john-luan/SDR-dongle/hardware/PL_Config.kicad_sch

## KiCad design hardware/PL_Config.kicad_sch (2022-02-24)

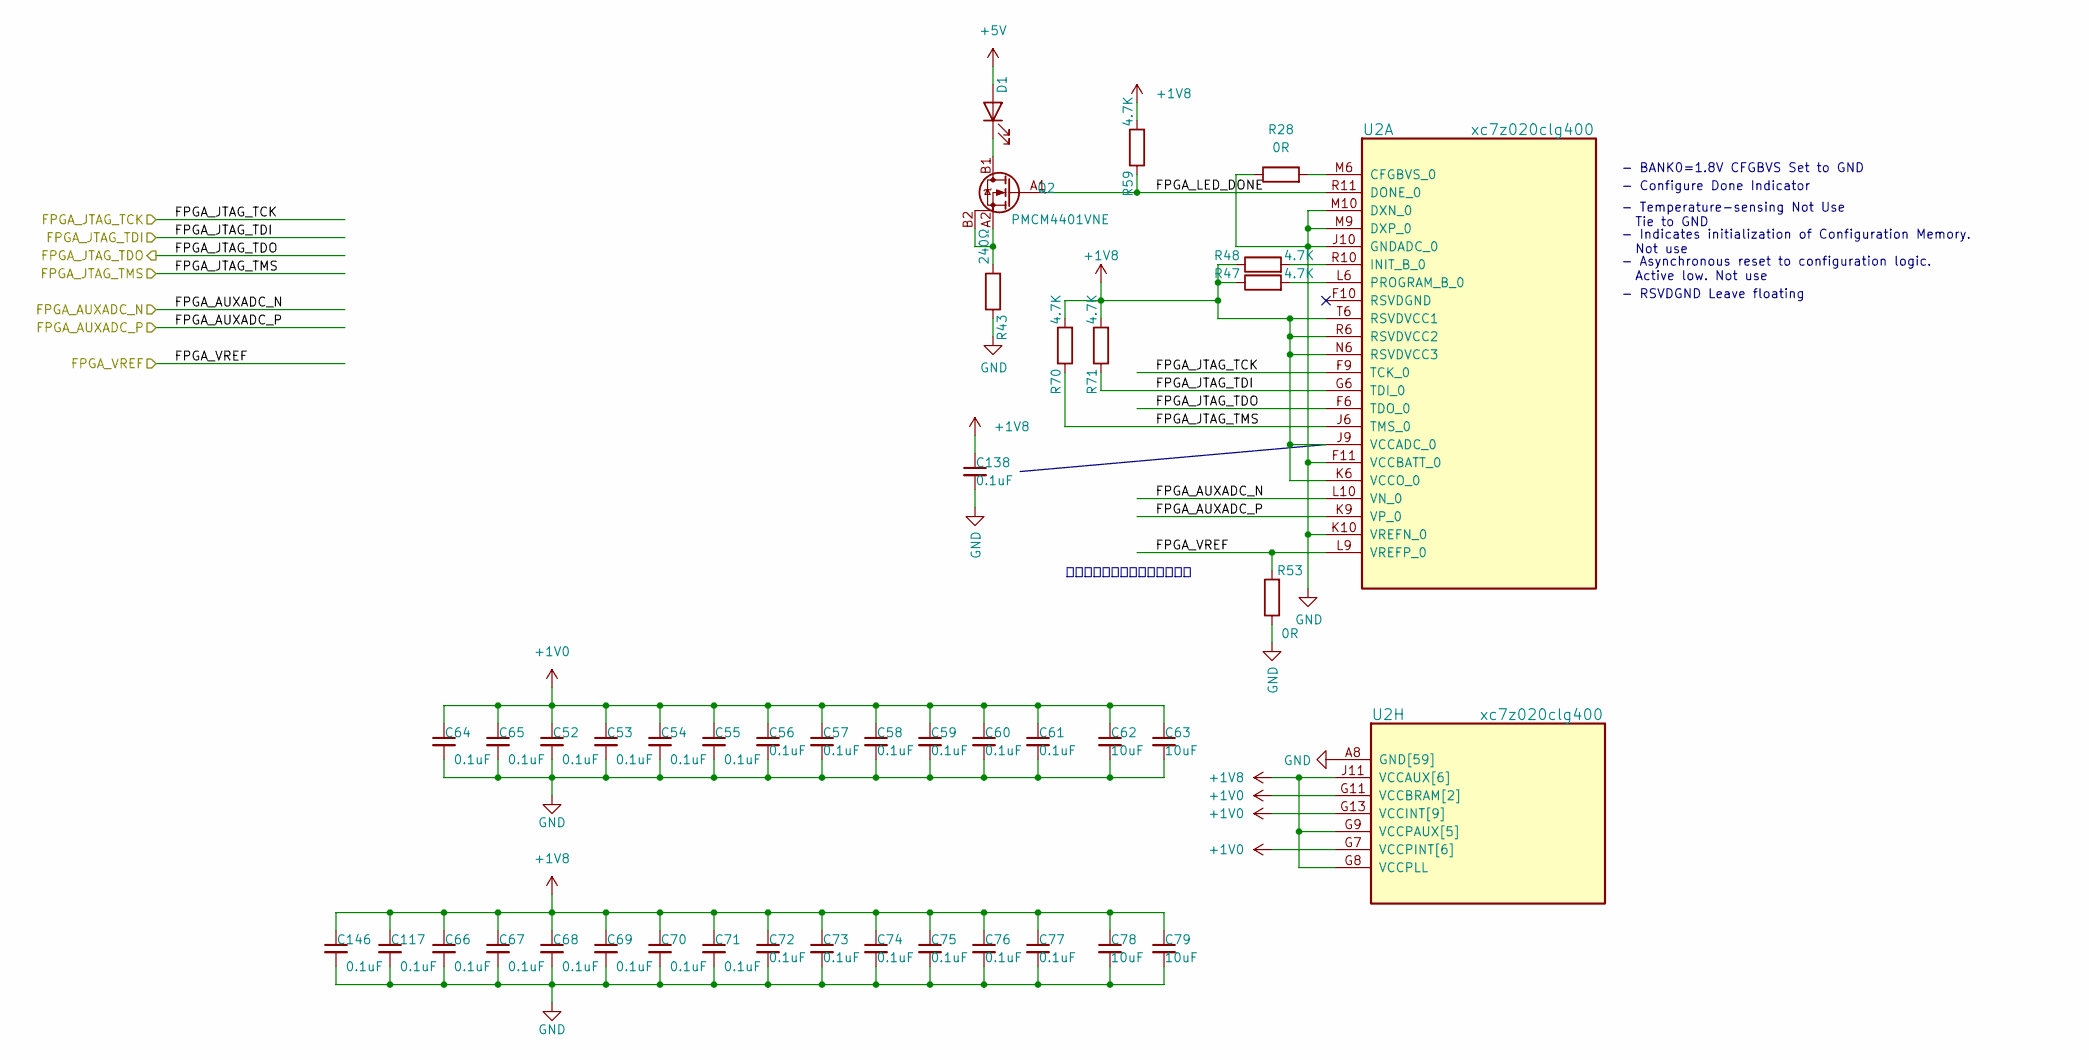
[picture p23: schematic PL_Config.kicad_sch]

Parts:
C52, C53, C54, C55, C56, C57, C58, C59, C60, C61, C64, C65, C66, C67, C68, C69, C70, C71, C72, C73, C74, C75, C76, C77, C117, C138, C146: 0.1uF; C_0201_0603Metric
C62, C63, C78, C79: 10uF; C_0402_1005Metric
D1: LED; LED_0201_0603Metric
Q2: PMCM4401VNE; WLCSP-4-X1-WLB0909-4_0.89x0.89mm_P0.5mm
R28, R53: 0R; R_0201_0603Metric
R43: 240Ω; R_0201_0603Metric
R47, R48, R59, R70, R71: 4.7K; R_0201_0603Metric
U2: xc7z020clg400; Xilinx_CLG400_020_Delay

Connections:
+1V0: C52.1, C53.1, C54.1, C55.1, C56.1, C57.1, C58.1, C59.1, C60.1, C61.1, C62.1, C63.1, C64.1, C65.1, U2.G7 (VCCPINT[6]), U2.G11 (VCCBRAM[2]), U2.G13 (VCCINT[9]), U2.H10 (VCCBRAM[2]), U2.H12 (VCCINT[9]), U2.J7 (VCCPINT[6]), U2.J13 (VCCINT[9]), U2.K12 (VCCINT[9]), U2.L7 (VCCPINT[6]), U2.L13 (VCCINT[9]), U2.M12 (VCCINT[9]), U2.N7 (VCCPINT[6]), U2.N13 (VCCINT[9]), U2.P8 (VCCPINT[6]), U2.P12 (VCCINT[9]), U2.R7 (VCCPINT[6]), U2.R13 (VCCINT[9])
+1V8: C66.1, C67.1, C68.1, C69.1, C70.1, C71.1, C72.1, C73.1, C74.1, C75.1, C76.1, C77.1, C78.1, C79.1, C117.1, C138.1, C146.1, R47.1, R48.1, R59.2, R70.2, R71.2, U2.F8 (VCCPAUX[5]), U2.G8 (VCCPLL), U2.G9 (VCCPAUX[5]), U2.H8 (VCCPAUX[5]), U2.J9 (VCCADC_0), U2.J11 (VCCAUX[6]), U2.K6 (VCCO_0), U2.K8 (VCCPAUX[5]), U2.L11 (VCCAUX[6]), U2.M8 (VCCPAUX[5]), U2.N6 (RSVDVCC3), U2.N9 (VCCAUX[6]), U2.N11 (VCCAUX[6]), U2.P10 (VCCAUX[6]), U2.R6 (RSVDVCC2), U2.R9 (VCCAUX[6]), U2.T6 (RSVDVCC1)
+5V: D1.2 (A)
FPGA_AUXADC_N: U2.L10 (VN_0)
FPGA_AUXADC_P: U2.K9 (VP_0)
FPGA_JTAG_TCK: U2.F9 (TCK_0)
FPGA_JTAG_TDI: R71.1, U2.G6 (TDI_0)
FPGA_JTAG_TDO: U2.F6 (TDO_0)
FPGA_JTAG_TMS: R70.1, U2.J6 (TMS_0)
FPGA_LED_DONE: Q2.A1 (G), R59.1, U2.R11 (DONE_0)
FPGA_VREF: R53.2, U2.L9 (VREFP_0)
GND: C52.2, C53.2, C54.2, C55.2, C56.2, C57.2, C58.2, C59.2, C60.2, C61.2, C62.2, C63.2, C64.2, C65.2, C66.2, C67.2, C68.2, C69.2, C70.2, C71.2, C72.2, C73.2, C74.2, C75.2, C76.2, C77.2, C78.2, C79.2, C117.2, C138.2, C146.2, R28.1, R43.1, R53.1, U2.A8 (GND[59]), U2.A18 (GND[59]), U2.B1 (GND[59]), U2.B11 (GND[59]), U2.C4 (GND[59]), U2.C9 (GND[59]), U2.C14 (GND[59]), U2.D17 (GND[59]), U2.E10 (GND[59]), U2.E20 (GND[59]), U2.F3 (GND[59]), U2.F7 (GND[59]), U2.F11 (VCCBATT_0), U2.G10 (GND[59]), U2.G12 (GND[59]), U2.G16 (GND[59]), U2.H7 (GND[59]), U2.H9 (GND[59]), U2.H11 (GND[59]), U2.H13 (GND[59]), U2.H19 (GND[59]), U2.J2 (GND[59]), U2.J8 (GND[59]), U2.J10 (GNDADC_0), U2.J12 (GND[59]), U2.K5 (GND[59]), U2.K7 (GND[59]), U2.K10 (VREFN_0), U2.K11 (GND[59]), U2.K13 (GND[59]), U2.K15 (GND[59]), U2.L8 (GND[59]), U2.L12 (GND[59]), U2.L18 (GND[59]), U2.M1 (GND[59]), U2.M7 (GND[59]), U2.M9 (DXP_0), U2.M10 (DXN_0), U2.M11 (GND[59]), U2.M13 (GND[59]), U2.N4 (GND[59]), U2.N8 (GND[59]), U2.N10 (GND[59]), U2.N12 (GND[59]), U2.N14 (GND[59]), U2.P7 (GND[59]), U2.P9 (GND[59]), U2.P11 (GND[59]), U2.P13 (GND[59]), U2.P17 (GND[59]), U2.R8 (GND[59]), U2.R12 (GND[59]), U2.R20 (GND[59]), U2.T3 (GND[59]), U2.T7 (GND[59]), U2.T13 (GND[59]), U2.U6 (GND[59]), U2.U16 (GND[59]), U2.V9 (GND[59]), U2.V19 (GND[59]), U2.W2 (GND[59]), U2.W12 (GND[59]), U2.Y5 (GND[59]), U2.Y15 (GND[59])
unnamed: D1.1 (K), Q2.B1 (D)
unnamed: Q2.A2 (S), Q2.B2 (D), R43.2
unnamed: R28.2, U2.M6 (CFGBVS_0)
unnamed: R47.2, U2.L6 (PROGRAM_B_0)
unnamed: R48.2, U2.R10 (INIT_B_0)

Notes on the sheet:
- RSVDGND Leave floating
- Configure Done Indicator
不用外部参考的时候怎么处理？
- Temperature-sensing Not Use Tie to GND
- Indicates initialization of Configuration Memory. Not use
- Asynchronous reset to configuration logic. Active low. Not use
- BANK0=1.8V CFGBVS Set to GND
