john-luan/SDR-dongle/hardware/PL_Connector.kicad_sch

## KiCad design hardware/PL_Connector.kicad_sch (2022-02-08)

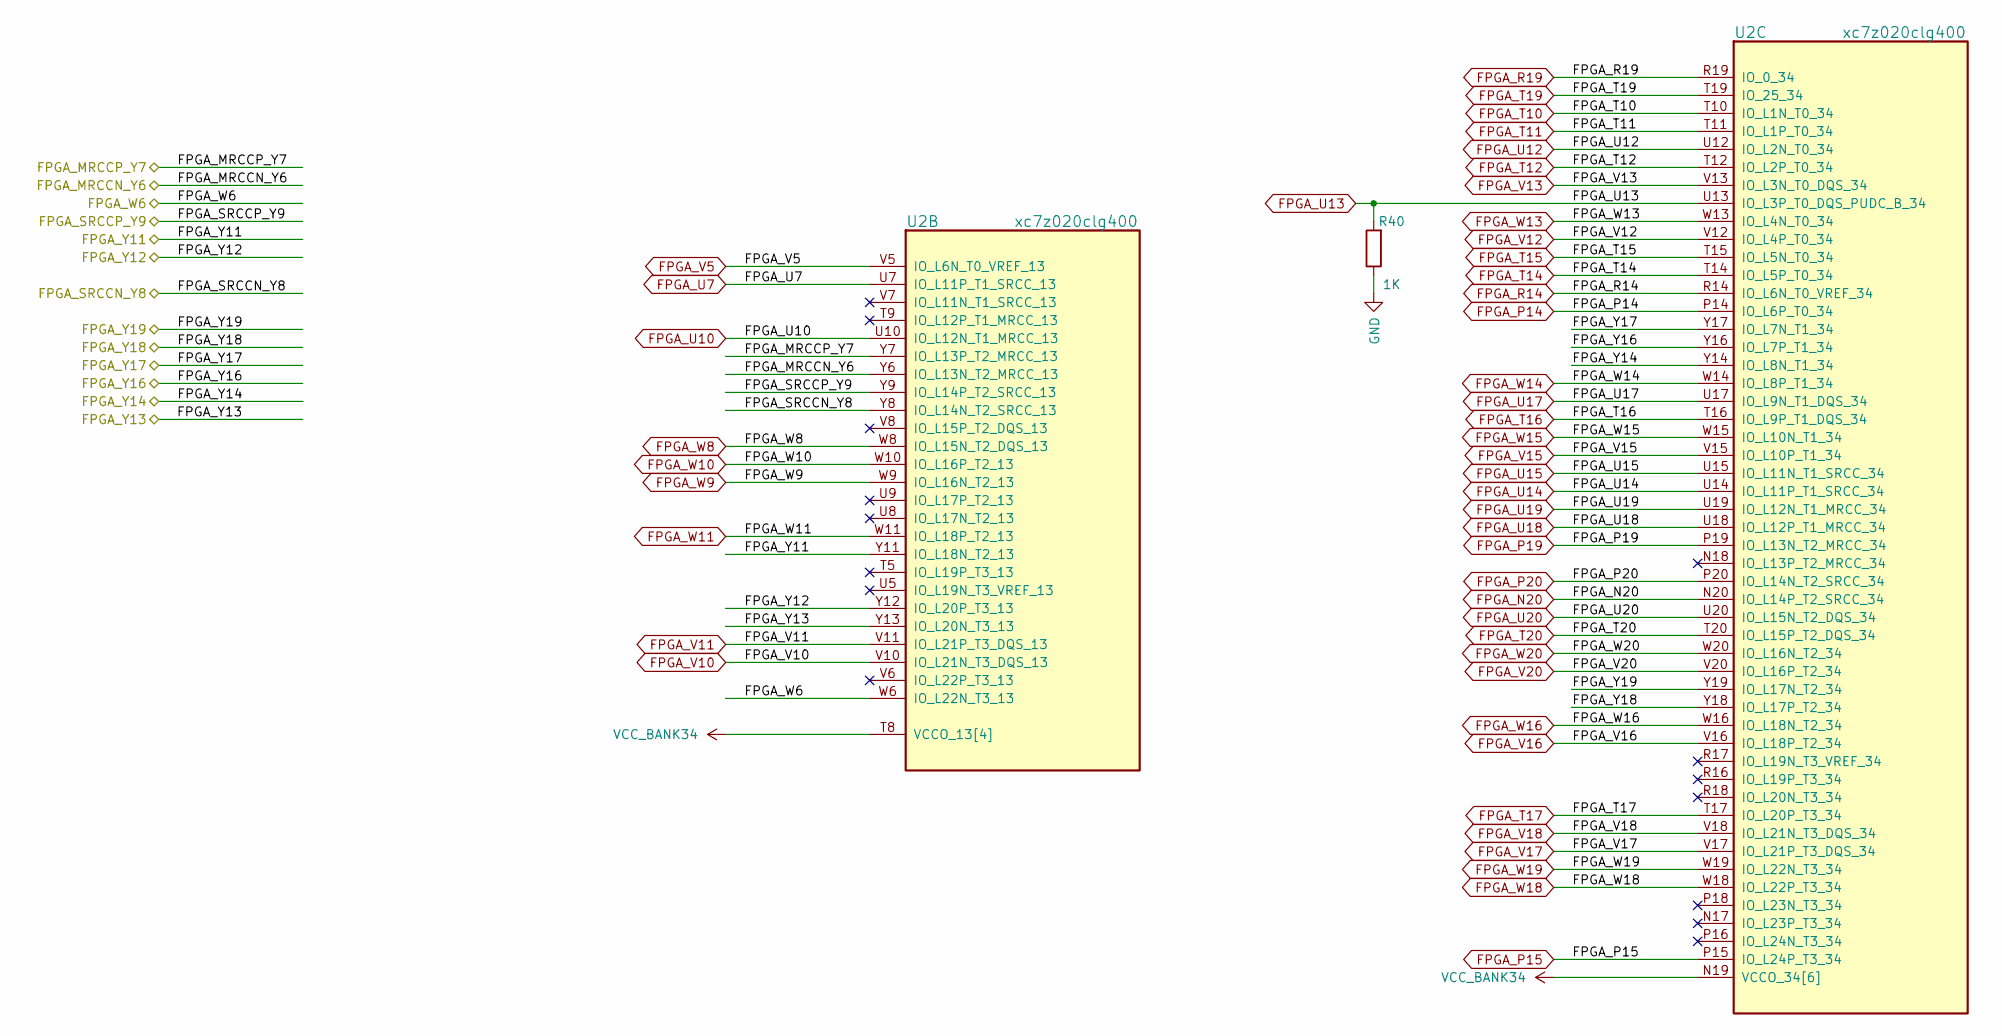
[picture p24: schematic PL_Connector.kicad_sch]

Parts:
R40: 1K; R_0201_0603Metric
U2: xc7z020clg400; Xilinx_CLG400_020_Delay

Connections:
FPGA_MRCCN_Y6: U2.Y6 (IO_L13N_T2_MRCC_13)
FPGA_MRCCP_Y7: U2.Y7 (IO_L13P_T2_MRCC_13)
FPGA_N20: U2.N20 (IO_L14P_T2_SRCC_34)
FPGA_P14: U2.P14 (IO_L6P_T0_34)
FPGA_P15: U2.P15 (IO_L24P_T3_34)
FPGA_P19: U2.P19 (IO_L13N_T2_MRCC_34)
FPGA_P20: U2.P20 (IO_L14N_T2_SRCC_34)
FPGA_R14: U2.R14 (IO_L6N_T0_VREF_34)
FPGA_R19: U2.R19 (IO_0_34)
FPGA_SRCCN_Y8: U2.Y8 (IO_L14N_T2_SRCC_13)
FPGA_SRCCP_Y9: U2.Y9 (IO_L14P_T2_SRCC_13)
FPGA_T10: U2.T10 (IO_L1N_T0_34)
FPGA_T11: U2.T11 (IO_L1P_T0_34)
FPGA_T12: U2.T12 (IO_L2P_T0_34)
FPGA_T14: U2.T14 (IO_L5P_T0_34)
FPGA_T15: U2.T15 (IO_L5N_T0_34)
FPGA_T16: U2.T16 (IO_L9P_T1_DQS_34)
FPGA_T17: U2.T17 (IO_L20P_T3_34)
FPGA_T19: U2.T19 (IO_25_34)
FPGA_T20: U2.T20 (IO_L15P_T2_DQS_34)
FPGA_U7: U2.U7 (IO_L11P_T1_SRCC_13)
FPGA_U10: U2.U10 (IO_L12N_T1_MRCC_13)
FPGA_U12: U2.U12 (IO_L2N_T0_34)
FPGA_U13: R40.2, U2.U13 (IO_L3P_T0_DQS_PUDC_B_34)
FPGA_U14: U2.U14 (IO_L11P_T1_SRCC_34)
FPGA_U15: U2.U15 (IO_L11N_T1_SRCC_34)
FPGA_U17: U2.U17 (IO_L9N_T1_DQS_34)
FPGA_U18: U2.U18 (IO_L12P_T1_MRCC_34)
FPGA_U19: U2.U19 (IO_L12N_T1_MRCC_34)
FPGA_U20: U2.U20 (IO_L15N_T2_DQS_34)
FPGA_V5: U2.V5 (IO_L6N_T0_VREF_13)
FPGA_V10: U2.V10 (IO_L21N_T3_DQS_13)
FPGA_V11: U2.V11 (IO_L21P_T3_DQS_13)
FPGA_V12: U2.V12 (IO_L4P_T0_34)
FPGA_V13: U2.V13 (IO_L3N_T0_DQS_34)
FPGA_V15: U2.V15 (IO_L10P_T1_34)
FPGA_V16: U2.V16 (IO_L18P_T2_34)
FPGA_V17: U2.V17 (IO_L21P_T3_DQS_34)
FPGA_V18: U2.V18 (IO_L21N_T3_DQS_34)
FPGA_V20: U2.V20 (IO_L16P_T2_34)
FPGA_W6: U2.W6 (IO_L22N_T3_13)
FPGA_W8: U2.W8 (IO_L15N_T2_DQS_13)
FPGA_W9: U2.W9 (IO_L16N_T2_13)
FPGA_W10: U2.W10 (IO_L16P_T2_13)
FPGA_W11: U2.W11 (IO_L18P_T2_13)
FPGA_W13: U2.W13 (IO_L4N_T0_34)
FPGA_W14: U2.W14 (IO_L8P_T1_34)
FPGA_W15: U2.W15 (IO_L10N_T1_34)
FPGA_W16: U2.W16 (IO_L18N_T2_34)
FPGA_W18: U2.W18 (IO_L22P_T3_34)
FPGA_W19: U2.W19 (IO_L22N_T3_34)
FPGA_W20: U2.W20 (IO_L16N_T2_34)
FPGA_Y11: U2.Y11 (IO_L18N_T2_13)
FPGA_Y12: U2.Y12 (IO_L20P_T3_13)
FPGA_Y13: U2.Y13 (IO_L20N_T3_13)
FPGA_Y14: U2.Y14 (IO_L8N_T1_34)
FPGA_Y16: U2.Y16 (IO_L7P_T1_34)
FPGA_Y17: U2.Y17 (IO_L7N_T1_34)
FPGA_Y18: U2.Y18 (IO_L17P_T2_34)
FPGA_Y19: U2.Y19 (IO_L17N_T2_34)
GND: R40.1
VCC_BANK34: U2.N19 (VCCO_34[6]), U2.R15 (VCCO_34[6]), U2.T8 (VCCO_13[4]), U2.T18 (VCCO_34[6]), U2.U11 (VCCO_13[4]), U2.V14 (VCCO_34[6]), U2.W7 (VCCO_13[4]), U2.W17 (VCCO_34[6]), U2.Y10 (VCCO_13[4]), U2.Y20 (VCCO_34[6])
