john-luan/SDR-dongle/hardware/PL_Transceiver.kicad_sch

## KiCad design hardware/PL_Transceiver.kicad_sch (2022-02-08)

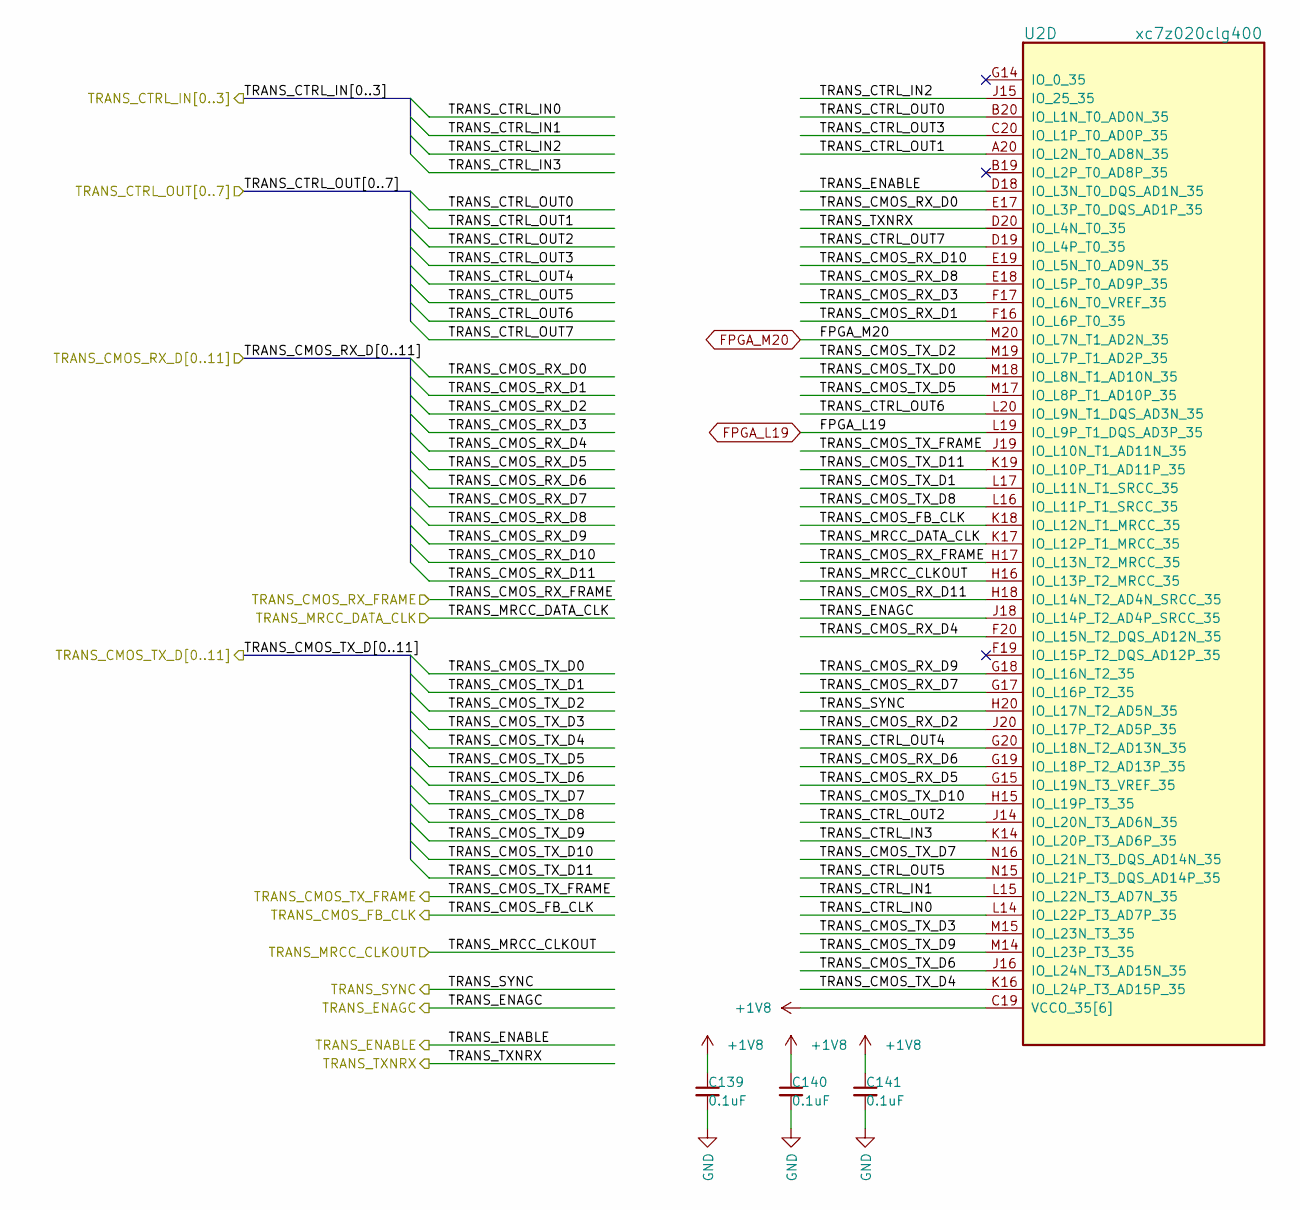
[picture p25: schematic PL_Transceiver.kicad_sch]

Parts:
C139, C140, C141: 0.1uF; C_0201_0603Metric
U2: xc7z020clg400; Xilinx_CLG400_020_Delay

Connections:
+1V8: C139.1, C140.1, C141.1, U2.C19 (VCCO_35[6]), U2.F18 (VCCO_35[6]), U2.H14 (VCCO_35[6]), U2.J17 (VCCO_35[6]), U2.K20 (VCCO_35[6]), U2.M16 (VCCO_35[6])
FPGA_L19: U2.L19 (IO_L9P_T1_DQS_AD3P_35)
FPGA_M20: U2.M20 (IO_L7N_T1_AD2N_35)
GND: C139.2, C140.2, C141.2
TRANS_CMOS_FB_CLK: U2.K18 (IO_L12N_T1_MRCC_35)
TRANS_CMOS_RX_D0: U2.E17 (IO_L3P_T0_DQS_AD1P_35)
TRANS_CMOS_RX_D1: U2.F16 (IO_L6P_T0_35)
TRANS_CMOS_RX_D2: U2.J20 (IO_L17P_T2_AD5P_35)
TRANS_CMOS_RX_D3: U2.F17 (IO_L6N_T0_VREF_35)
TRANS_CMOS_RX_D4: U2.F20 (IO_L15N_T2_DQS_AD12N_35)
TRANS_CMOS_RX_D5: U2.G15 (IO_L19N_T3_VREF_35)
TRANS_CMOS_RX_D6: U2.G19 (IO_L18P_T2_AD13P_35)
TRANS_CMOS_RX_D7: U2.G17 (IO_L16P_T2_35)
TRANS_CMOS_RX_D8: U2.E18 (IO_L5P_T0_AD9P_35)
TRANS_CMOS_RX_D9: U2.G18 (IO_L16N_T2_35)
TRANS_CMOS_RX_D10: U2.E19 (IO_L5N_T0_AD9N_35)
TRANS_CMOS_RX_D11: U2.H18 (IO_L14N_T2_AD4N_SRCC_35)
TRANS_CMOS_RX_FRAME: U2.H17 (IO_L13N_T2_MRCC_35)
TRANS_CMOS_TX_D0: U2.M18 (IO_L8N_T1_AD10N_35)
TRANS_CMOS_TX_D1: U2.L17 (IO_L11N_T1_SRCC_35)
TRANS_CMOS_TX_D2: U2.M19 (IO_L7P_T1_AD2P_35)
TRANS_CMOS_TX_D3: U2.M15 (IO_L23N_T3_35)
TRANS_CMOS_TX_D4: U2.K16 (IO_L24P_T3_AD15P_35)
TRANS_CMOS_TX_D5: U2.M17 (IO_L8P_T1_AD10P_35)
TRANS_CMOS_TX_D6: U2.J16 (IO_L24N_T3_AD15N_35)
TRANS_CMOS_TX_D7: U2.N16 (IO_L21N_T3_DQS_AD14N_35)
TRANS_CMOS_TX_D8: U2.L16 (IO_L11P_T1_SRCC_35)
TRANS_CMOS_TX_D9: U2.M14 (IO_L23P_T3_35)
TRANS_CMOS_TX_D10: U2.H15 (IO_L19P_T3_35)
TRANS_CMOS_TX_D11: U2.K19 (IO_L10P_T1_AD11P_35)
TRANS_CMOS_TX_FRAME: U2.J19 (IO_L10N_T1_AD11N_35)
TRANS_CTRL_IN0: U2.L14 (IO_L22P_T3_AD7P_35)
TRANS_CTRL_IN1: U2.L15 (IO_L22N_T3_AD7N_35)
TRANS_CTRL_IN2: U2.J15 (IO_25_35)
TRANS_CTRL_IN3: U2.K14 (IO_L20P_T3_AD6P_35)
TRANS_CTRL_OUT0: U2.B20 (IO_L1N_T0_AD0N_35)
TRANS_CTRL_OUT1: U2.A20 (IO_L2N_T0_AD8N_35)
TRANS_CTRL_OUT2: U2.J14 (IO_L20N_T3_AD6N_35)
TRANS_CTRL_OUT3: U2.C20 (IO_L1P_T0_AD0P_35)
TRANS_CTRL_OUT4: U2.G20 (IO_L18N_T2_AD13N_35)
TRANS_CTRL_OUT5: U2.N15 (IO_L21P_T3_DQS_AD14P_35)
TRANS_CTRL_OUT6: U2.L20 (IO_L9N_T1_DQS_AD3N_35)
TRANS_CTRL_OUT7: U2.D19 (IO_L4P_T0_35)
TRANS_ENABLE: U2.D18 (IO_L3N_T0_DQS_AD1N_35)
TRANS_ENAGC: U2.J18 (IO_L14P_T2_AD4P_SRCC_35)
TRANS_MRCC_CLKOUT: U2.H16 (IO_L13P_T2_MRCC_35)
TRANS_MRCC_DATA_CLK: U2.K17 (IO_L12P_T1_MRCC_35)
TRANS_SYNC: U2.H20 (IO_L17N_T2_AD5N_35)
TRANS_TXNRX: U2.D20 (IO_L4N_T0_35)
