john-luan/SDR-dongle/hardware/PS_Config.kicad_sch

## KiCad design hardware/PS_Config.kicad_sch (2022-02-24)

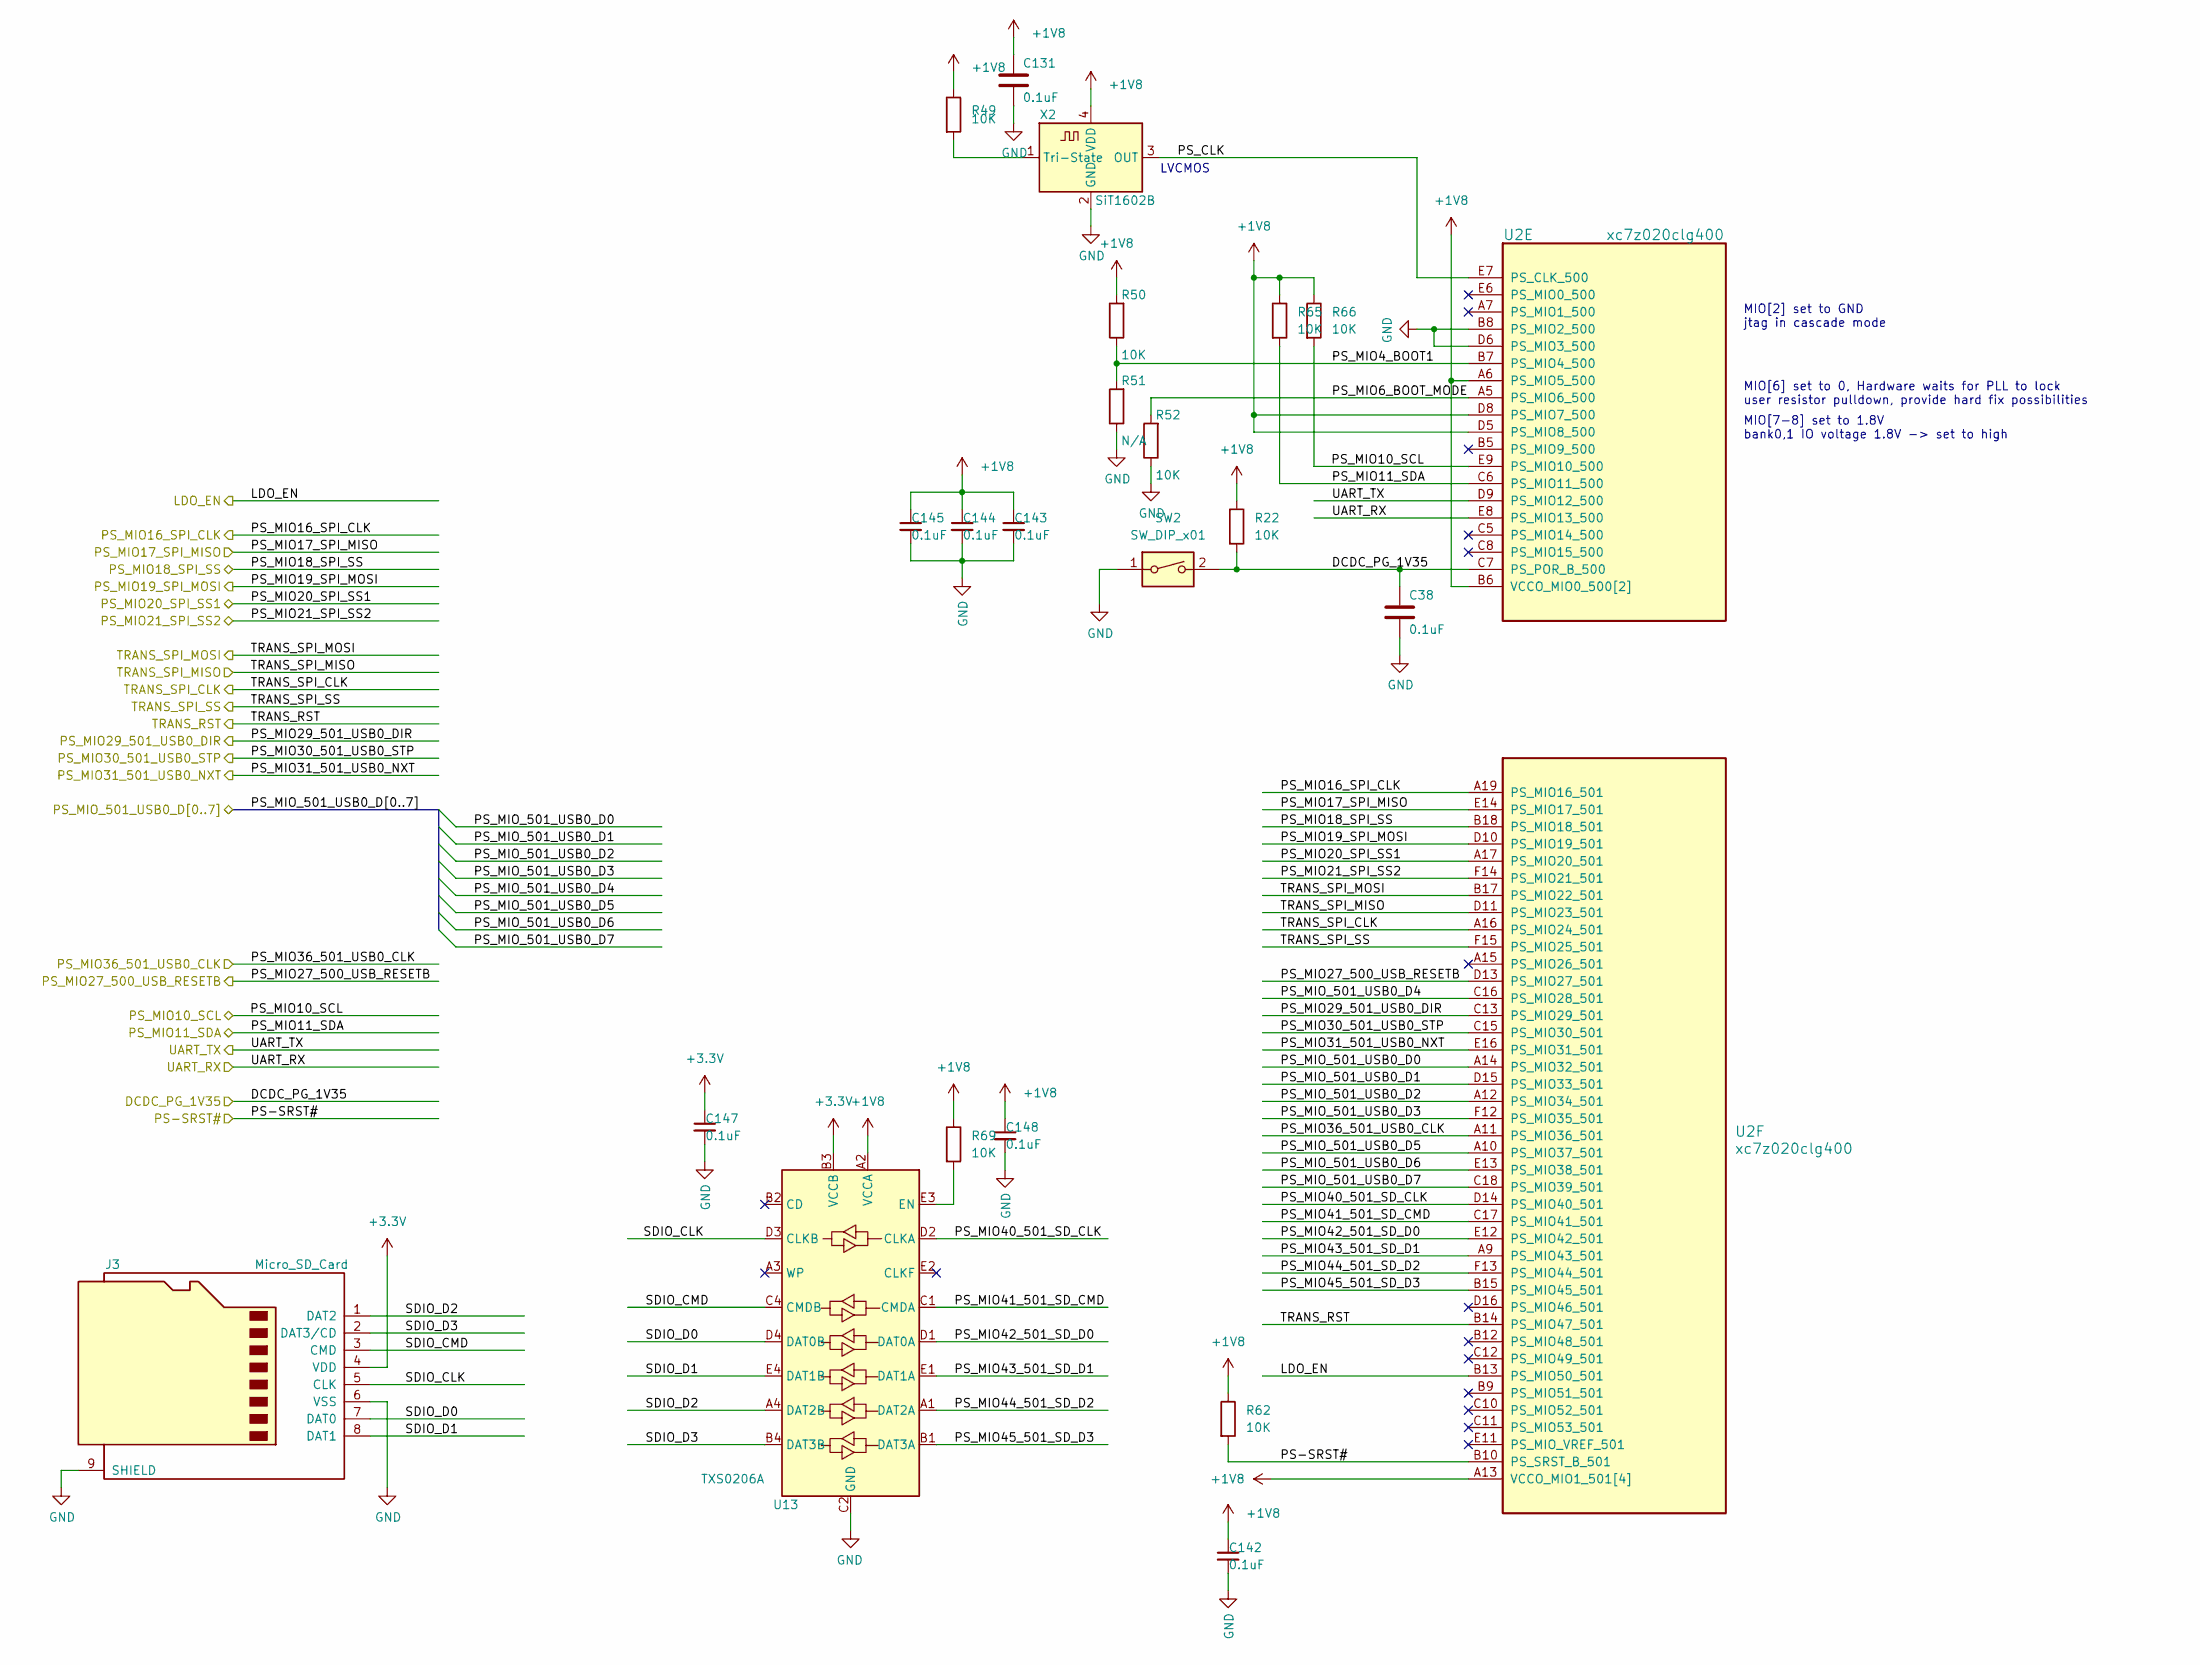
[picture p26: schematic PS_Config.kicad_sch]

Parts:
C38, C131, C142, C143, C144, C145, C147, C148: 0.1uF; C_0201_0603Metric
J3: Micro_SD_Card; microSD_HC_Molex_104031-0811
R22, R49, R50, R52, R62, R65, R66, R69: 10K; R_0201_0603Metric
R51: N/A; R_0201_0603Metric
SW2: SW_DIP_x01; EVQ9P701P
U2: xc7z020clg400; Xilinx_CLG400_020_Delay
U13: TXS0206A; WLCSP-20_1.609x1.994mm_Layout4x5_P0.4mm
X2: SiT1602B; Oscillator_SMD_ECS_2520MV-xxx-xx-4Pin_2.5x2.0mm

Connections:
+1V8: C131.1, C142.1, C143.1, C144.1, C145.1, C148.1, R22.1, R49.1, R50.2, R62.1, R65.1, R66.1, R69.1, U2.A6 (PS_MIO5_500), U2.A13 (VCCO_MIO1_501[4]), U2.B6 (VCCO_MIO0_500[2]), U2.B16 (VCCO_MIO1_501[4]), U2.D5 (PS_MIO8_500), U2.D7 (VCCO_MIO0_500[2]), U2.D8 (PS_MIO7_500), U2.D12 (VCCO_MIO1_501[4]), U2.E15 (VCCO_MIO1_501[4]), U13.A2 (VCCA), X2.4 (VDD)
+3.3V: C147.1, J3.4 (VDD), U13.B3 (VCCB)
DCDC_PG_1V35: C38.1, R22.2, SW2.2, U2.C7 (PS_POR_B_500)
GND: C38.2, C131.2, C142.2, C143.2, C144.2, C145.2, C147.2, C148.2, J3.6 (VSS), J3.9 (SHIELD), R51.1, R52.1, SW2.1, U2.B8 (PS_MIO2_500), U2.D6 (PS_MIO3_500), U13.C2 (GND), U13.C3 (GND), X2.2 (GND)
LDO_EN: U2.B13 (PS_MIO50_501)
unnamed: R49.2, X2.1 (Tri-State)
unnamed: R69.2, U13.E3 (EN)
PS-SRST#: R62.2, U2.B10 (PS_SRST_B_501)
PS_CLK: U2.E7 (PS_CLK_500), X2.3 (OUT)
PS_MIO4_BOOT1: R50.1, R51.2, U2.B7 (PS_MIO4_500)
PS_MIO6_BOOT_MODE: R52.2, U2.A5 (PS_MIO6_500)
PS_MIO10_SCL: R66.2, U2.E9 (PS_MIO10_500)
PS_MIO11_SDA: R65.2, U2.C6 (PS_MIO11_500)
PS_MIO16_SPI_CLK: U2.A19 (PS_MIO16_501)
PS_MIO17_SPI_MISO: U2.E14 (PS_MIO17_501)
PS_MIO18_SPI_SS: U2.B18 (PS_MIO18_501)
PS_MIO19_SPI_MOSI: U2.D10 (PS_MIO19_501)
PS_MIO20_SPI_SS1: U2.A17 (PS_MIO20_501)
PS_MIO21_SPI_SS2: U2.F14 (PS_MIO21_501)
PS_MIO27_500_USB_RESETB: U2.D13 (PS_MIO27_501)
PS_MIO29_501_USB0_DIR: U2.C13 (PS_MIO29_501)
PS_MIO30_501_USB0_STP: U2.C15 (PS_MIO30_501)
PS_MIO31_501_USB0_NXT: U2.E16 (PS_MIO31_501)
PS_MIO36_501_USB0_CLK: U2.A11 (PS_MIO36_501)
PS_MIO40_501_SD_CLK: U2.D14 (PS_MIO40_501), U13.D2 (CLKA)
PS_MIO41_501_SD_CMD: U2.C17 (PS_MIO41_501), U13.C1 (CMDA)
PS_MIO42_501_SD_D0: U2.E12 (PS_MIO42_501), U13.D1 (DAT0A)
PS_MIO43_501_SD_D1: U2.A9 (PS_MIO43_501), U13.E1 (DAT1A)
PS_MIO44_501_SD_D2: U2.F13 (PS_MIO44_501), U13.A1 (DAT2A)
PS_MIO45_501_SD_D3: U2.B15 (PS_MIO45_501), U13.B1 (DAT3A)
PS_MIO_501_USB0_D0: U2.A14 (PS_MIO32_501)
PS_MIO_501_USB0_D1: U2.D15 (PS_MIO33_501)
PS_MIO_501_USB0_D2: U2.A12 (PS_MIO34_501)
PS_MIO_501_USB0_D3: U2.F12 (PS_MIO35_501)
PS_MIO_501_USB0_D4: U2.C16 (PS_MIO28_501)
PS_MIO_501_USB0_D5: U2.A10 (PS_MIO37_501)
PS_MIO_501_USB0_D6: U2.E13 (PS_MIO38_501)
PS_MIO_501_USB0_D7: U2.C18 (PS_MIO39_501)
SDIO_CLK: J3.5 (CLK), U13.D3 (CLKB)
SDIO_CMD: J3.3 (CMD), U13.C4 (CMDB)
SDIO_D0: J3.7 (DAT0), U13.D4 (DAT0B)
SDIO_D1: J3.8 (DAT1), U13.E4 (DAT1B)
SDIO_D2: J3.1 (DAT2), U13.A4 (DAT2B)
SDIO_D3: J3.2 (DAT3/CD), U13.B4 (DAT3B)
TRANS_RST: U2.B14 (PS_MIO47_501)
TRANS_SPI_CLK: U2.A16 (PS_MIO24_501)
TRANS_SPI_MISO: U2.D11 (PS_MIO23_501)
TRANS_SPI_MOSI: U2.B17 (PS_MIO22_501)
TRANS_SPI_SS: U2.F15 (PS_MIO25_501)
UART_RX: U2.E8 (PS_MIO13_500)
UART_TX: U2.D9 (PS_MIO12_500)

Notes on the sheet:
MIO[6] set to 0, Hardware waits for PLL to lock user resistor pulldown, provide hard fix possibilities
MIO[7-8] set to 1.8V bank0,1 IO voltage 1.8V -> set to high
LVCMOS
MIO[2] set to GND jtag in cascade mode
