john-luan/SDR-dongle/hardware/PS_DDR.kicad_sch

## KiCad design hardware/PS_DDR.kicad_sch (2022-02-24)

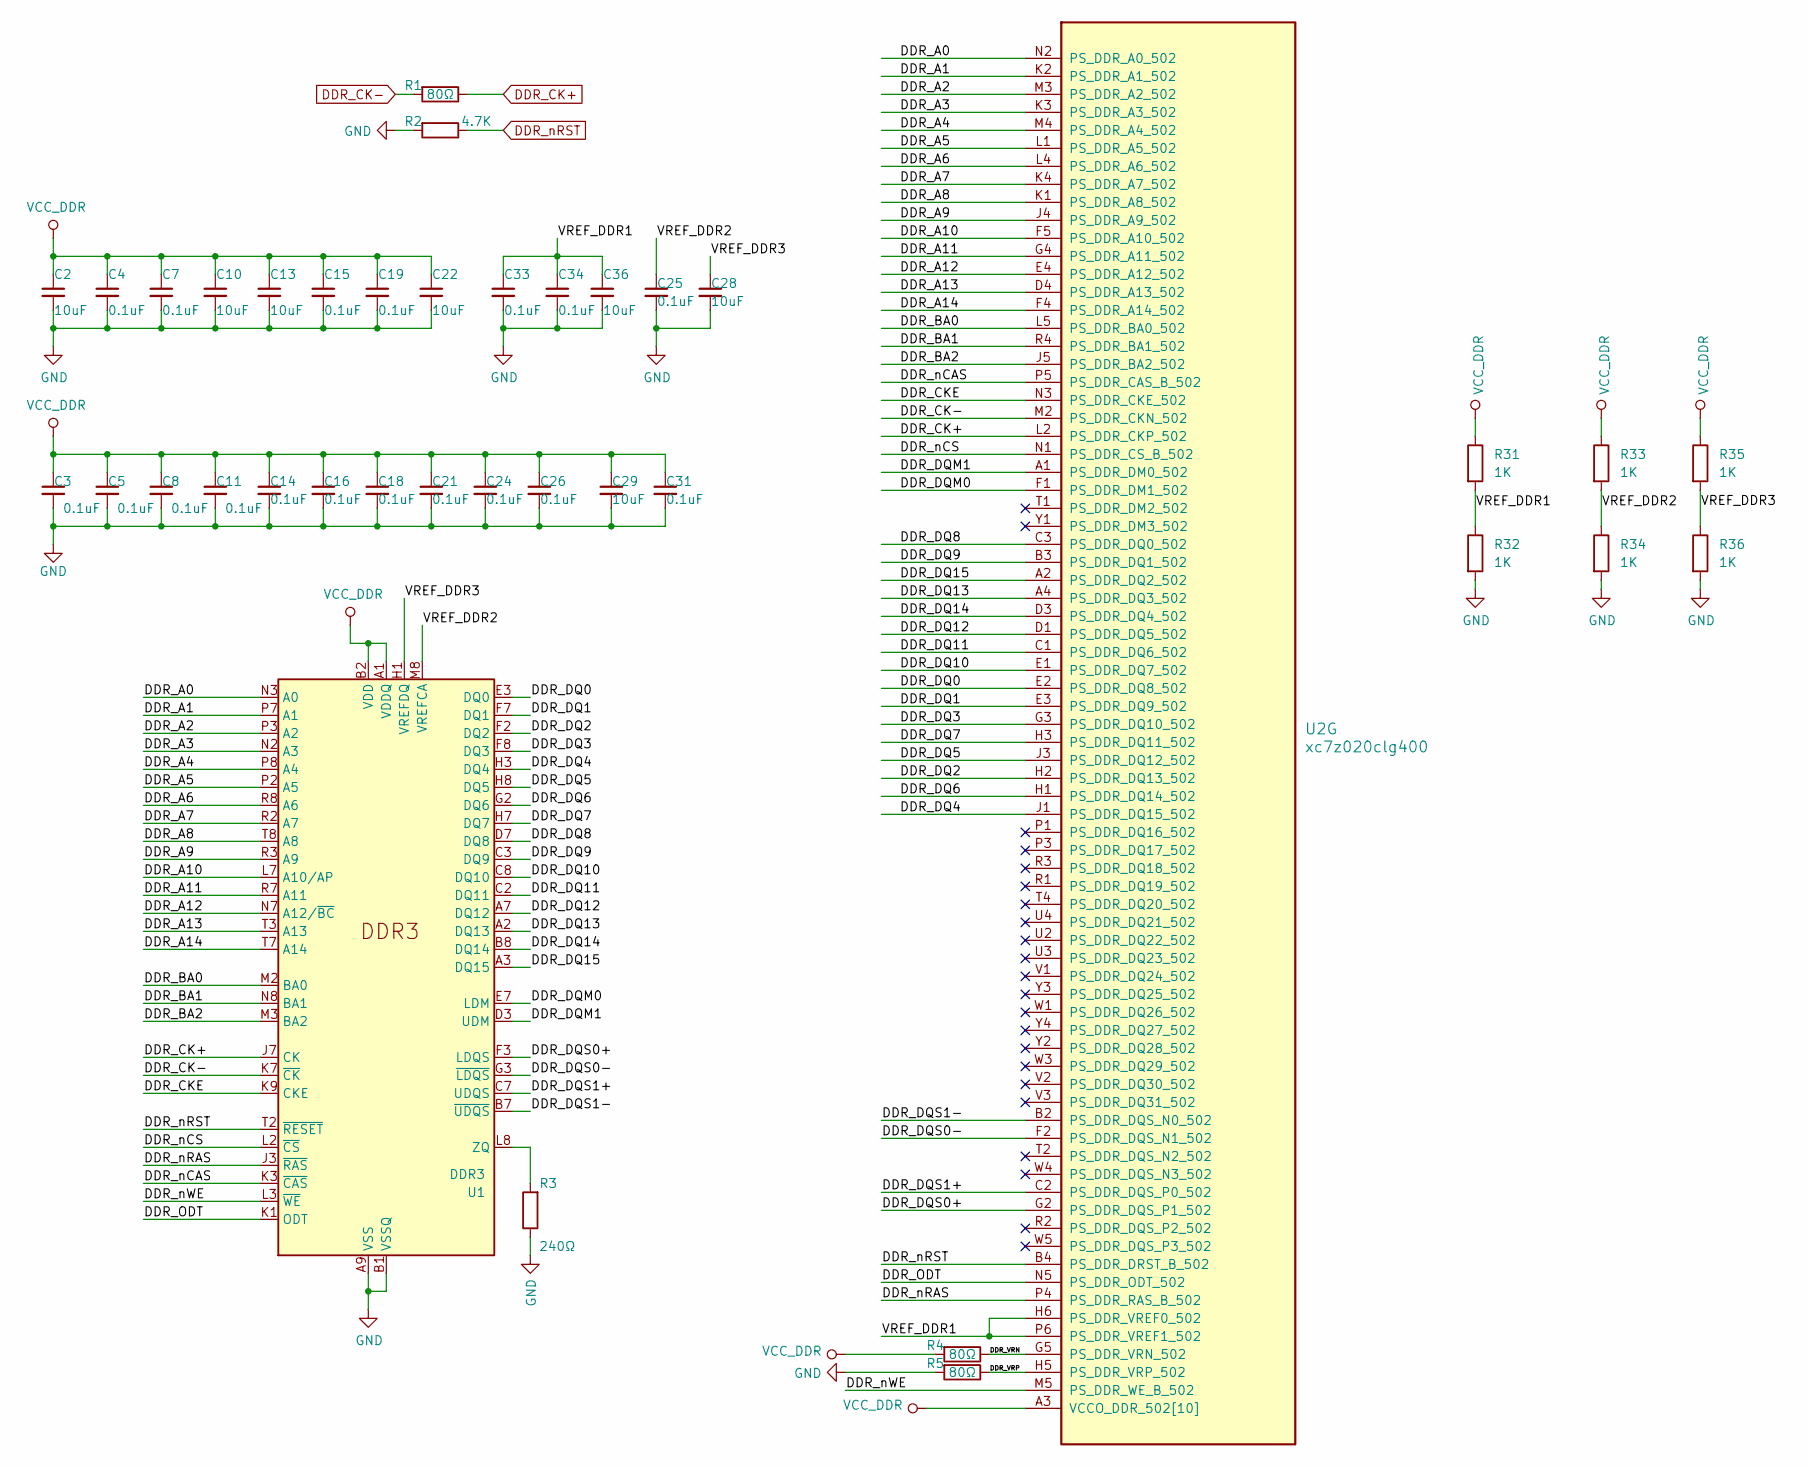
[picture p27: schematic PS_DDR.kicad_sch]

Parts:
C2, C10, C13, C22, C28, C29, C36: 10uF; C_0402_1005Metric
C3, C4, C5, C7, C8, C11, C14, C15, C16, C18, C19, C21, C24, C25, C26, C31, C33, C34: 0.1uF; C_0201_0603Metric
R1, R4, R5: 80Ω; R_0201_0603Metric
R2: 4.7K; R_0201_0603Metric
R3: 240Ω; R_0201_0603Metric
R31, R32, R33, R34, R35, R36: 1K; R_0201_0603Metric
U1: DDR3; BGA-96_9.0x13.0mm_Layout2x3x16_P0.8mm_NoPaste
U2: xc7z020clg400; Xilinx_CLG400_020_Delay

Connections:
DDR_A0: U1.N3 (A0), U2.N2 (PS_DDR_A0_502)
DDR_A1: U1.P7 (A1), U2.K2 (PS_DDR_A1_502)
DDR_A2: U1.P3 (A2), U2.M3 (PS_DDR_A2_502)
DDR_A3: U1.N2 (A3), U2.K3 (PS_DDR_A3_502)
DDR_A4: U1.P8 (A4), U2.M4 (PS_DDR_A4_502)
DDR_A5: U1.P2 (A5), U2.L1 (PS_DDR_A5_502)
DDR_A6: U1.R8 (A6), U2.L4 (PS_DDR_A6_502)
DDR_A7: U1.R2 (A7), U2.K4 (PS_DDR_A7_502)
DDR_A8: U1.T8 (A8), U2.K1 (PS_DDR_A8_502)
DDR_A9: U1.R3 (A9), U2.J4 (PS_DDR_A9_502)
DDR_A10: U1.L7 (A10/AP), U2.F5 (PS_DDR_A10_502)
DDR_A11: U1.R7 (A11), U2.G4 (PS_DDR_A11_502)
DDR_A12: U1.N7 (A12/~BC), U2.E4 (PS_DDR_A12_502)
DDR_A13: U1.T3 (A13), U2.D4 (PS_DDR_A13_502)
DDR_A14: U1.T7 (A14), U2.F4 (PS_DDR_A14_502)
DDR_BA0: U1.M2 (BA0), U2.L5 (PS_DDR_BA0_502)
DDR_BA1: U1.N8 (BA1), U2.R4 (PS_DDR_BA1_502)
DDR_BA2: U1.M3 (BA2), U2.J5 (PS_DDR_BA2_502)
DDR_CK+: R1.1, U1.J7 (CK), U2.L2 (PS_DDR_CKP_502)
DDR_CK-: R1.2, U1.K7 (~CK), U2.M2 (PS_DDR_CKN_502)
DDR_CKE: U1.K9 (CKE), U2.N3 (PS_DDR_CKE_502)
DDR_DQ0: U1.E3 (DQ0), U2.E2 (PS_DDR_DQ8_502)
DDR_DQ1: U1.F7 (DQ1), U2.E3 (PS_DDR_DQ9_502)
DDR_DQ2: U1.F2 (DQ2), U2.H2 (PS_DDR_DQ13_502)
DDR_DQ3: U1.F8 (DQ3), U2.G3 (PS_DDR_DQ10_502)
DDR_DQ4: U1.H3 (DQ4), U2.J1 (PS_DDR_DQ15_502)
DDR_DQ5: U1.H8 (DQ5), U2.J3 (PS_DDR_DQ12_502)
DDR_DQ6: U1.G2 (DQ6), U2.H1 (PS_DDR_DQ14_502)
DDR_DQ7: U1.H7 (DQ7), U2.H3 (PS_DDR_DQ11_502)
DDR_DQ8: U1.D7 (DQ8), U2.C3 (PS_DDR_DQ0_502)
DDR_DQ9: U1.C3 (DQ9), U2.B3 (PS_DDR_DQ1_502)
DDR_DQ10: U1.C8 (DQ10), U2.E1 (PS_DDR_DQ7_502)
DDR_DQ11: U1.C2 (DQ11), U2.C1 (PS_DDR_DQ6_502)
DDR_DQ12: U1.A7 (DQ12), U2.D1 (PS_DDR_DQ5_502)
DDR_DQ13: U1.A2 (DQ13), U2.A4 (PS_DDR_DQ3_502)
DDR_DQ14: U1.B8 (DQ14), U2.D3 (PS_DDR_DQ4_502)
DDR_DQ15: U1.A3 (DQ15), U2.A2 (PS_DDR_DQ2_502)
DDR_DQM0: U1.E7 (LDM), U2.F1 (PS_DDR_DM1_502)
DDR_DQM1: U1.D3 (UDM), U2.A1 (PS_DDR_DM0_502)
DDR_DQS0+: U1.F3 (LDQS), U2.G2 (PS_DDR_DQS_P1_502)
DDR_DQS0-: U1.G3 (~LDQS), U2.F2 (PS_DDR_DQS_N1_502)
DDR_DQS1+: U1.C7 (UDQS), U2.C2 (PS_DDR_DQS_P0_502)
DDR_DQS1-: U1.B7 (~UDQS), U2.B2 (PS_DDR_DQS_N0_502)
DDR_ODT: U1.K1 (ODT), U2.N5 (PS_DDR_ODT_502)
DDR_VRN: R4.1, U2.G5 (PS_DDR_VRN_502)
DDR_VRP: R5.1, U2.H5 (PS_DDR_VRP_502)
DDR_nCAS: U1.K3 (~CAS), U2.P5 (PS_DDR_CAS_B_502)
DDR_nCS: U1.L2 (~CS), U2.N1 (PS_DDR_CS_B_502)
DDR_nRAS: U1.J3 (~RAS), U2.P4 (PS_DDR_RAS_B_502)
DDR_nRST: R2.1, U1.T2 (~RESET), U2.B4 (PS_DDR_DRST_B_502)
DDR_nWE: U1.L3 (~WE), U2.M5 (PS_DDR_WE_B_502)
GND: C2.2, C3.2, C4.2, C5.2, C7.2, C8.2, C10.2, C11.2, C13.2, C14.2, C15.2, C16.2, C18.2, C19.2, C21.2, C22.2, C24.2, C25.2, C26.2, C28.2, C29.2, C31.2, C33.2, C34.2, C36.2, R2.2, R3.1, R5.2, R32.2, R34.2, R36.2, U1.A9 (VSS), U1.B1 (VSSQ), U1.B3 (VSS), U1.B9 (VSSQ), U1.D1 (VSSQ), U1.D8 (VSSQ), U1.E1 (VSS), U1.E2 (VSSQ), U1.E8 (VSSQ), U1.F9 (VSSQ), U1.G1 (VSSQ), U1.G8 (VSS), U1.G9 (VSSQ), U1.J2 (VSS), U1.J8 (VSS), U1.M1 (VSS), U1.M9 (VSS), U1.P1 (VSS), U1.P9 (VSS), U1.T1 (VSS), U1.T9 (VSS)
unnamed: R3.2, U1.L8 (ZQ)
VCC_DDR: C2.1, C3.1, C4.1, C5.1, C7.1, C8.1, C10.1, C11.1, C13.1, C14.1, C15.1, C16.1, C18.1, C19.1, C21.1, C22.1, C24.1, C26.1, C29.1, C31.1, R4.2, R31.1, R33.1, R35.1, U1.A1 (VDDQ), U1.A8 (VDDQ), U1.B2 (VDD), U1.C1 (VDDQ), U1.C9 (VDDQ), U1.D2 (VDDQ), U1.D9 (VDD), U1.E9 (VDDQ), U1.F1 (VDDQ), U1.G7 (VDD), U1.H2 (VDDQ), U1.H9 (VDDQ), U1.K2 (VDD), U1.K8 (VDD), U1.N1 (VDD), U1.N9 (VDD), U1.R1 (VDD), U1.R9 (VDD), U2.A3 (VCCO_DDR_502[10]), U2.D2 (VCCO_DDR_502[10]), U2.E5 (VCCO_DDR_502[10]), U2.G1 (VCCO_DDR_502[10]), U2.H4 (VCCO_DDR_502[10]), U2.L3 (VCCO_DDR_502[10]), U2.P2 (VCCO_DDR_502[10]), U2.R5 (VCCO_DDR_502[10]), U2.U1 (VCCO_DDR_502[10]), U2.V4 (VCCO_DDR_502[10])
VREF_DDR1: C33.1, C34.1, C36.1, R31.2, R32.1, U2.H6 (PS_DDR_VREF0_502), U2.P6 (PS_DDR_VREF1_502)
VREF_DDR2: C25.1, R33.2, R34.1, U1.M8 (VREFCA)
VREF_DDR3: C28.1, R35.2, R36.1, U1.H1 (VREFDQ)
