john-luan/SDR-dongle/hardware/Power_Manage.kicad_sch

## KiCad design hardware/Power_Manage.kicad_sch (2022-02-24)

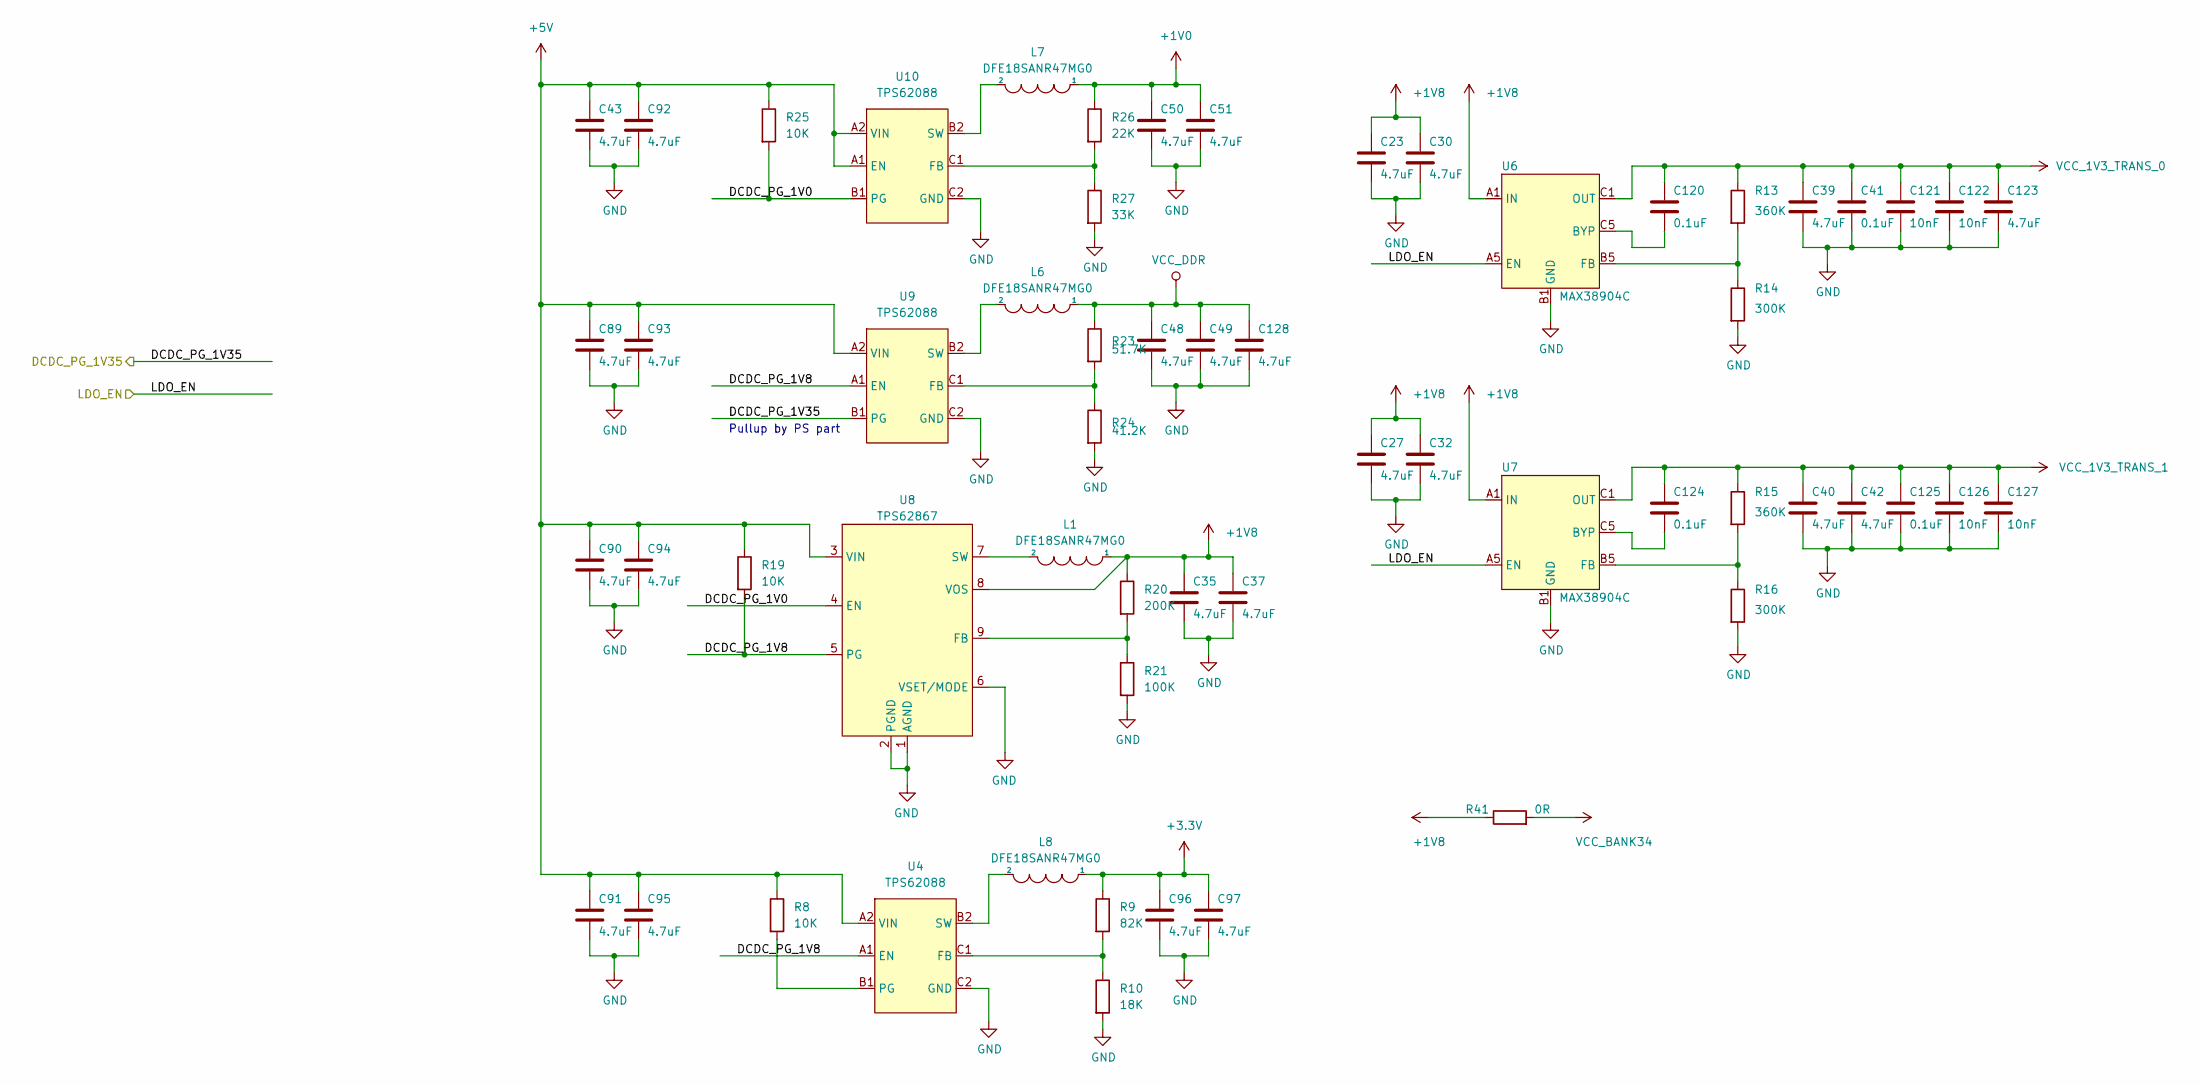
[picture p28: schematic Power_Manage.kicad_sch]

Parts:
C23, C27, C30, C32, C35, C37, C39, C40, C42, C43, C48, C49, C50, C51, C89, C90, C91, C92, C93, C94, C95, C96, C97, C123, C128: 4.7uF; C_0402_1005Metric
C41, C120, C124, C125: 0.1uF; C_0402_1005Metric
C121, C122, C126, C127: 10nF; C_0402_1005Metric
L1, L6, L7, L8: DFE18SANR47MG0; L_Murata_LQH2MCNxxxx02_2.0x1.6mm
R8, R19, R25: 10K; R_0201_0603Metric
R9: 82K; R_0201_0603Metric
R10: 18K; R_0201_0603Metric
R13, R15: 360K; R_0201_0603Metric
R14, R16: 300K; R_0201_0603Metric
R20: 200K; R_0201_0603Metric
R21: 100K; R_0201_0603Metric
R23: 51.7K; R_0201_0603Metric
R24: 41.2K; R_0201_0603Metric
R26: 22K; R_0201_0603Metric
R27: 33K; R_0201_0603Metric
R41: 0R; R_0402_1005Metric
U4, U9, U10: TPS62088; PowerWCSP-6
U6, U7: MAX38904C; wlp-15_2p168_1p338_0p5_0p4
U8: TPS62867; VQFN-HR

Connections:
+1V0: C50.1, C51.1, L7.1, R26.1
+1V8: C23.1, C27.1, C30.1, C32.1, C35.1, C37.1, L1.1, R20.1, R41.1, U6.A1 (IN), U6.A2 (IN), U6.A3 (IN), U6.A4 (IN), U7.A1 (IN), U7.A2 (IN), U7.A3 (IN), U7.A4 (IN), U8.8 (VOS)
+3.3V: C96.1, C97.1, L8.1, R9.1
+5V: C43.1, C89.1, C90.1, C91.1, C92.1, C93.1, C94.1, C95.1, R8.1, R19.1, R25.1, U4.A2 (VIN), U8.3 (VIN), U9.A2 (VIN), U10.A1 (EN), U10.A2 (VIN)
DCDC_PG_1V0: R25.2, U8.4 (EN), U10.B1 (PG)
DCDC_PG_1V8: R19.2, U4.A1 (EN), U8.5 (PG), U9.A1 (EN)
DCDC_PG_1V35: U9.B1 (PG)
GND: C23.2, C27.2, C30.2, C32.2, C35.2, C37.2, C39.2, C40.2, C41.2, C42.2, C43.2, C48.2, C49.2, C50.2, C51.2, C89.2, C90.2, C91.2, C92.2, C93.2, C94.2, C95.2, C96.2, C97.2, C121.2, C122.2, C123.2, C125.2, C126.2, C127.2, C128.2, R10.2, R14.2, R16.2, R21.2, R24.2, R27.2, U4.C2 (GND), U6.B1 (GND), U6.B2 (GND), U6.B3 (GND), U6.B4 (GND), U7.B1 (GND), U7.B2 (GND), U7.B3 (GND), U7.B4 (GND), U8.1 (AGND), U8.2 (PGND), U8.6 (VSET/MODE), U9.C2 (GND), U10.C2 (GND)
LDO_EN: U6.A5 (EN), U7.A5 (EN)
unnamed: C120.2, U6.C5 (BYP)
unnamed: C124.2, U7.C5 (BYP)
unnamed: L1.2, U8.7 (SW)
unnamed: L6.2, U9.B2 (SW)
unnamed: L7.2, U10.B2 (SW)
unnamed: L8.2, U4.B2 (SW)
unnamed: R8.2, U4.B1 (PG)
unnamed: R9.2, R10.1, U4.C1 (FB)
unnamed: R13.2, R14.1, U6.B5 (FB)
unnamed: R15.2, R16.1, U7.B5 (FB)
unnamed: R20.2, R21.1, U8.9 (FB)
unnamed: R23.2, R24.1, U9.C1 (FB)
unnamed: R26.2, R27.1, U10.C1 (FB)
VCC_1V3_TRANS_0: C39.1, C41.1, C120.1, C121.1, C122.1, C123.1, R13.1, U6.C1 (OUT), U6.C2 (OUT), U6.C3 (OUT), U6.C4 (OUT)
VCC_1V3_TRANS_1: C40.1, C42.1, C124.1, C125.1, C126.1, C127.1, R15.1, U7.C1 (OUT), U7.C2 (OUT), U7.C3 (OUT), U7.C4 (OUT)
VCC_BANK34: R41.2
VCC_DDR: C48.1, C49.1, C128.1, L6.1, R23.1

Notes on the sheet:
Pullup by PS part
