john-luan/SDR-dongle/hardware/Transceiver_Power.kicad_sch

## KiCad design hardware/Transceiver_Power.kicad_sch (2022-02-08)

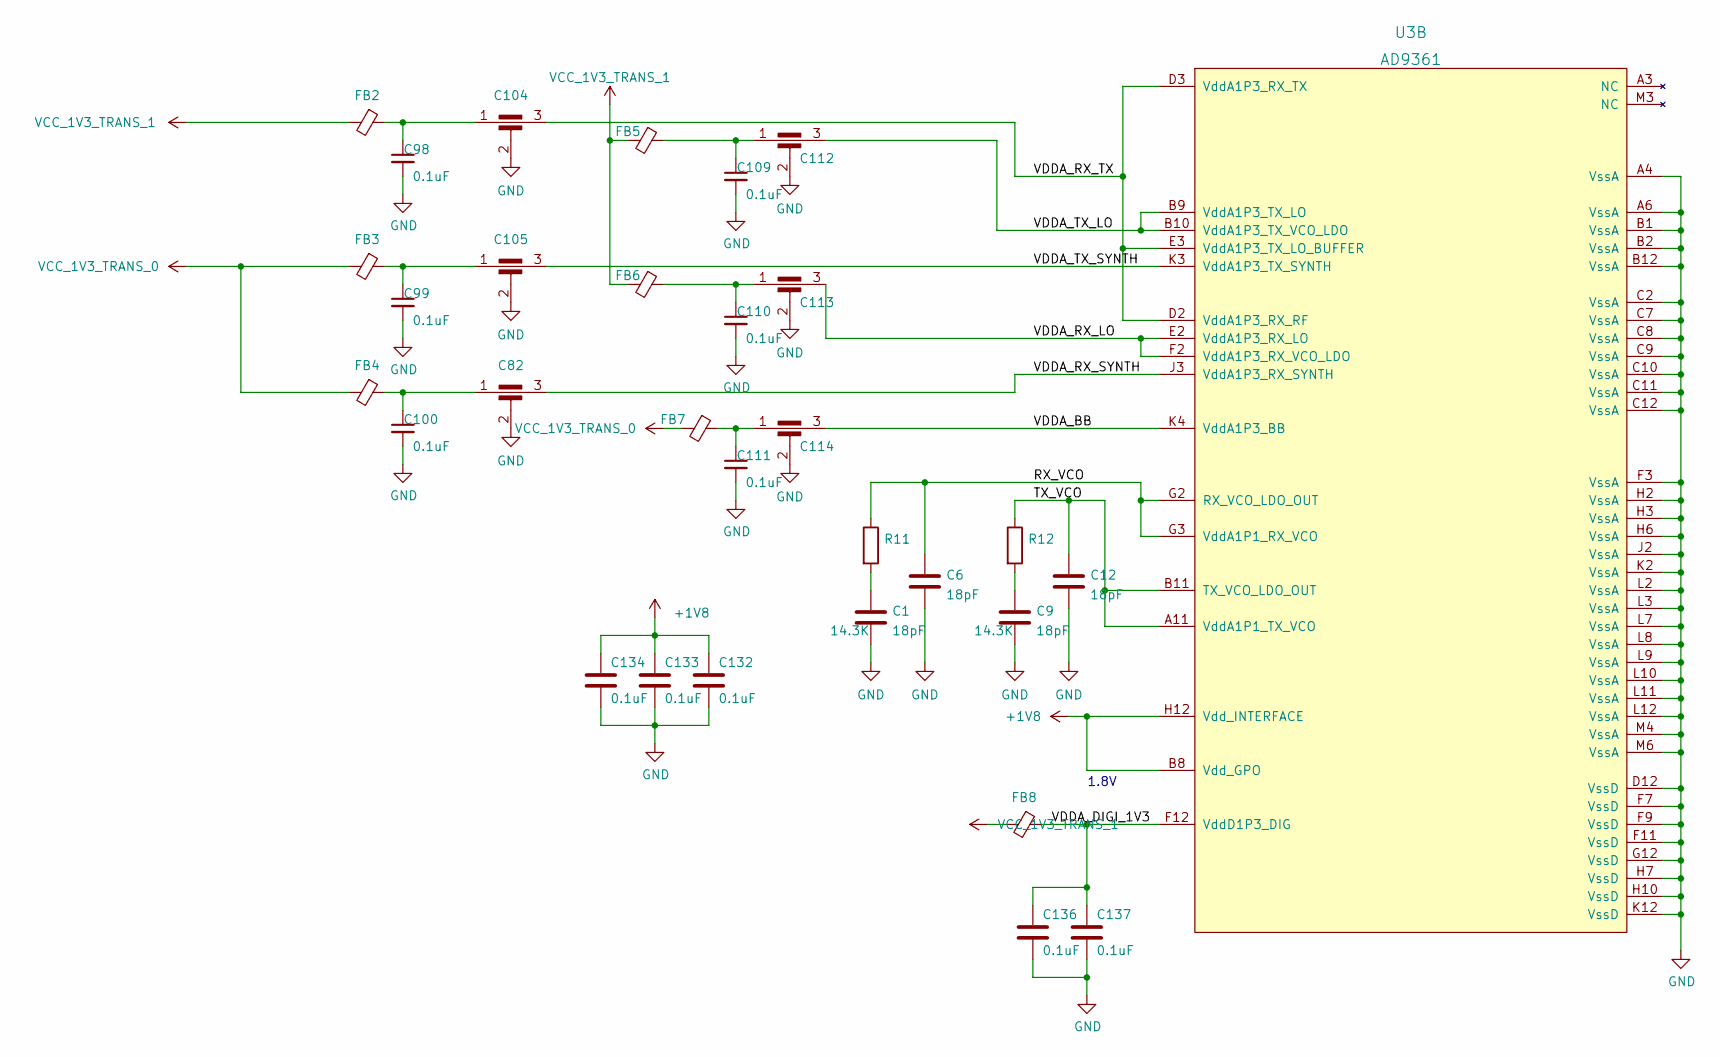
[picture p29: schematic Transceiver_Power.kicad_sch]

Parts:
C1, C6, C9, C12: 18pF; C_0201_0603Metric
C82, C104, C105, C112, C113, C114: NFM15PC146R0G3D; C_0402_1005Metric
C98, C99, C100, C109, C110, C111, C132, C133, C134, C136, C137: 0.1uF; C_0201_0603Metric
FB2, FB3, FB4, FB5, FB6, FB7, FB8: FerriteBead_Small; C_0201_0603Metric
R11, R12: 14.3K; R_0201_0603Metric
U3: AD9361; bga-100_10_10_1p32_0p8

Connections:
+1V8: C132.1, C133.1, C134.1, U3.B8 (Vdd_GPO), U3.H12 (Vdd_INTERFACE)
GND: C1.2, C6.2, C9.2, C12.2, C82.2, C98.2, C99.2, C100.2, C104.2, C105.2, C109.2, C110.2, C111.2, C112.2, C113.2, C114.2, C132.2, C133.2, C134.2, C136.2, C137.2, U3.A4 (VssA), U3.A6 (VssA), U3.B1 (VssA), U3.B2 (VssA), U3.B12 (VssA), U3.C2 (VssA), U3.C7 (VssA), U3.C8 (VssA), U3.C9 (VssA), U3.C10 (VssA), U3.C11 (VssA), U3.C12 (VssA), U3.D12 (VssD), U3.F3 (VssA), U3.F7 (VssD), U3.F9 (VssD), U3.F11 (VssD), U3.G12 (VssD), U3.H2 (VssA), U3.H3 (VssA), U3.H6 (VssA), U3.H7 (VssD), U3.H10 (VssD), U3.J2 (VssA), U3.K2 (VssA), U3.K12 (VssD), U3.L2 (VssA), U3.L3 (VssA), U3.L7 (VssA), U3.L8 (VssA), U3.L9 (VssA), U3.L10 (VssA), U3.L11 (VssA), U3.L12 (VssA), U3.M4 (VssA), U3.M6 (VssA)
unnamed: C1.1, R11.2
unnamed: C9.1, R12.2
unnamed: C82.1, C100.1, FB4.1
unnamed: C98.1, C104.1, FB2.1
unnamed: C99.1, C105.1, FB3.1
unnamed: C109.1, C112.1, FB5.1
unnamed: C110.1, C113.1, FB6.1
unnamed: C111.1, C114.1, FB7.1
RX_VCO: C6.1, R11.1, U3.G2 (RX_VCO_LDO_OUT), U3.G3 (VddA1P1_RX_VCO)
TX_VCO: C12.1, R12.1, U3.A11 (VddA1P1_TX_VCO), U3.B11 (TX_VCO_LDO_OUT)
VCC_1V3_TRANS_0: FB3.2, FB4.2, FB7.2
VCC_1V3_TRANS_1: FB2.2, FB5.2, FB6.2, FB8.2
VDDA_BB: C114.3, U3.K4 (VddA1P3_BB)
VDDA_DIGI_1V3: C136.1, C137.1, FB8.1, U3.F12 (VddD1P3_DIG)
VDDA_RX_LO: C113.3, U3.E2 (VddA1P3_RX_LO), U3.F2 (VddA1P3_RX_VCO_LDO)
VDDA_RX_SYNTH: C82.3, U3.J3 (VddA1P3_RX_SYNTH)
VDDA_RX_TX: C104.3, U3.D2 (VddA1P3_RX_RF), U3.D3 (VddA1P3_RX_TX), U3.E3 (VddA1P3_TX_LO_BUFFER)
VDDA_TX_LO: C112.3, U3.B9 (VddA1P3_TX_LO), U3.B10 (VddA1P3_TX_VCO_LDO)
VDDA_TX_SYNTH: C105.3, U3.K3 (VddA1P3_TX_SYNTH)

Notes on the sheet:
1.8V
