john-luan/SDR-dongle/hardware/Transceiver_RF.kicad_sch

## KiCad design hardware/Transceiver_RF.kicad_sch (2022-02-09)

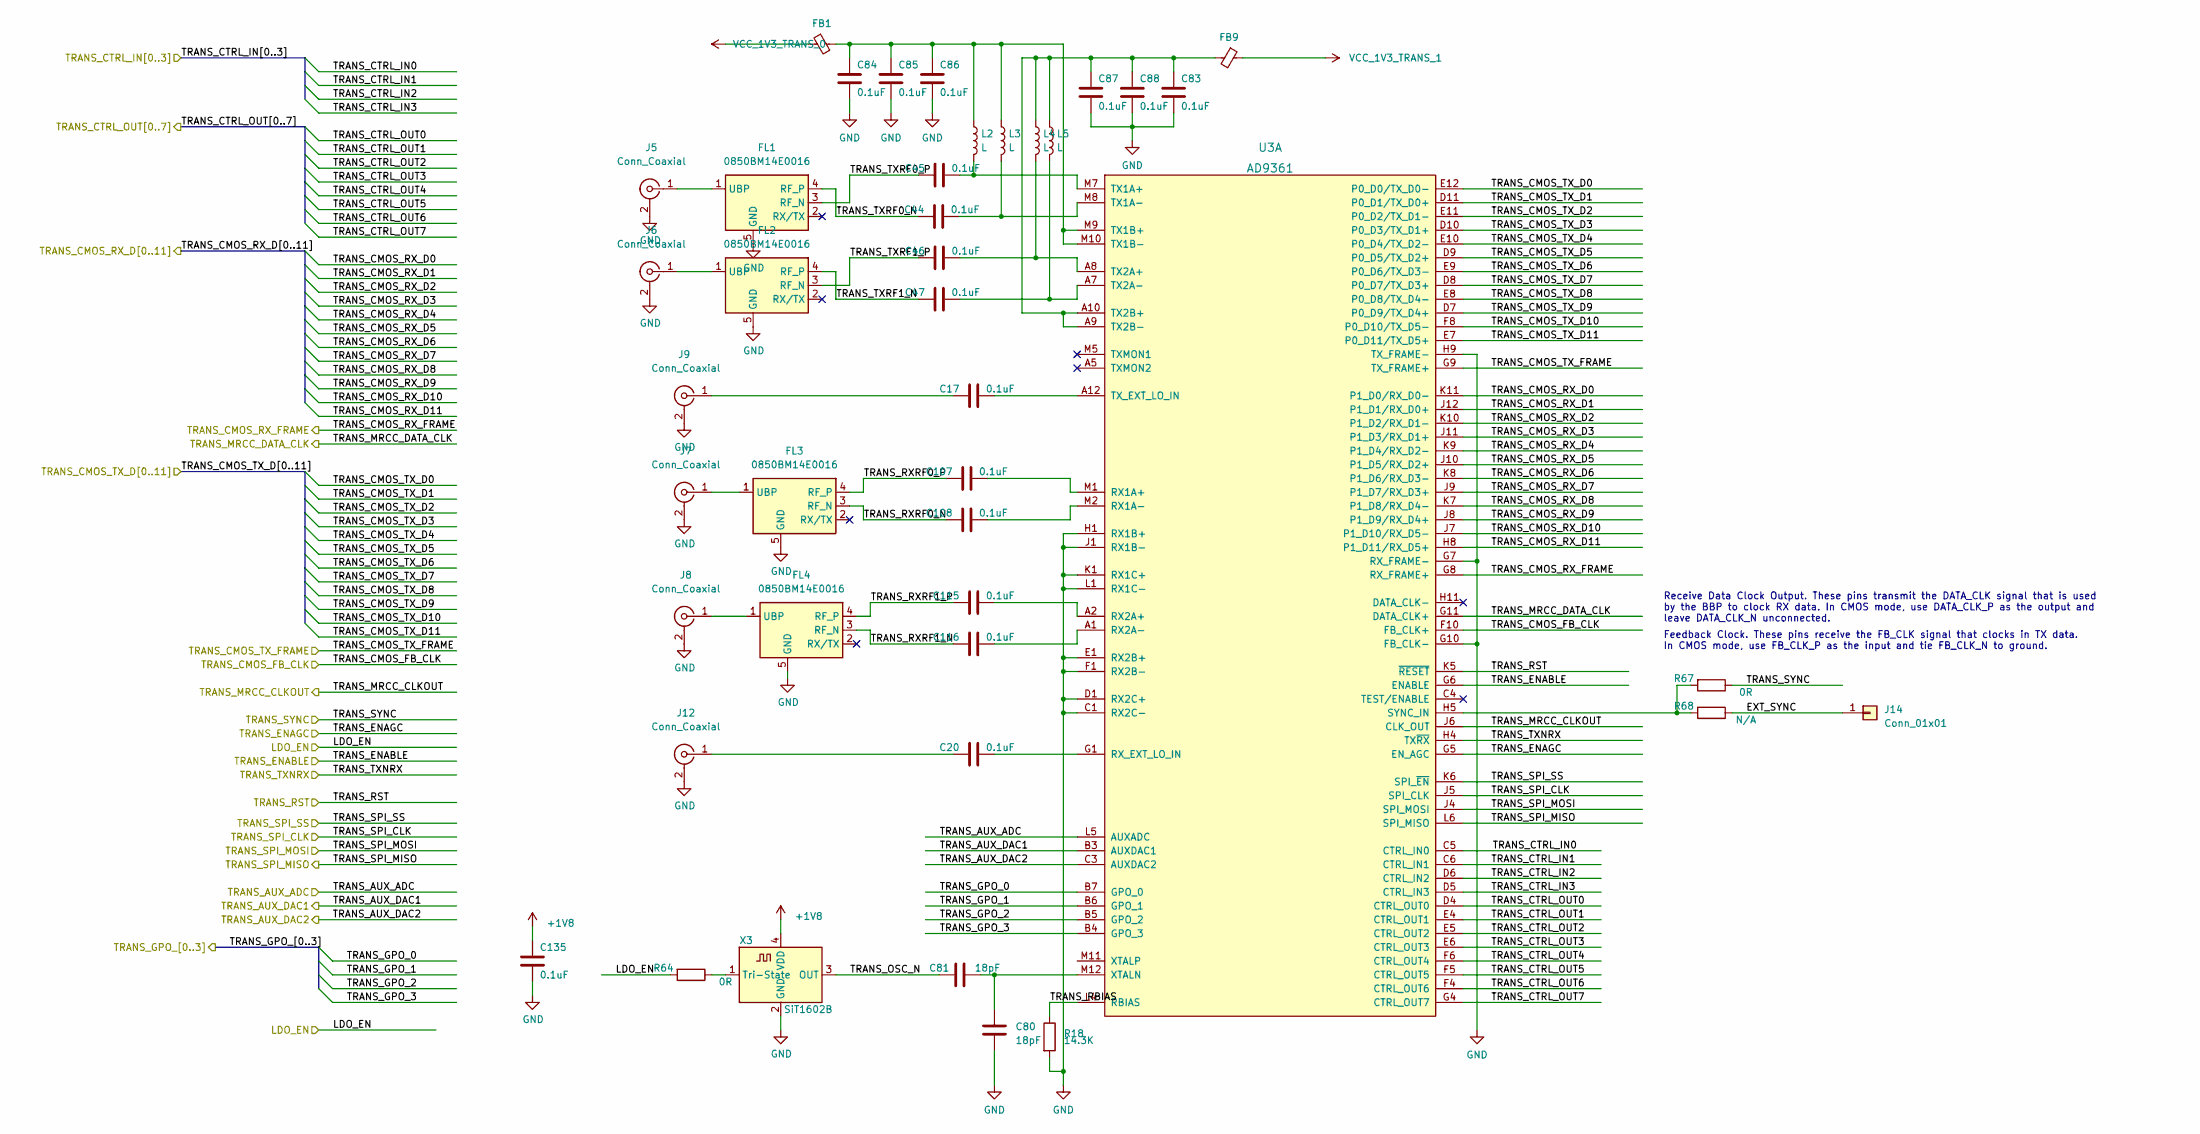
[picture p30: schematic Transceiver_RF.kicad_sch]

Parts:
C17, C20, C44, C45, C46, C47, C83, C84, C85, C86, C87, C88, C107, C108, C115, C116, C135: 0.1uF; C_0201_0603Metric
C80, C81: 18pF; C_0201_0603Metric
FB1, FB9: FerriteBead_Small; C_0402_1005Metric
FL1, FL2, FL3, FL4: 0850BM14E0016; Balun_Johanson_1.6x0.8mm
J5, J6, J7, J8, J9, J12: Conn_Coaxial; U.FL_Molex_MCRF_73412-0110_Vertical
J14: Conn_01x01; PinHeader_1x01_P2.54mm_Vertical
L2, L3, L4, L5: L; L_0402_1005Metric
R18: 14.3K; R_0201_0603Metric
R64, R67: 0R; R_0201_0603Metric
R68: N/A; R_0201_0603Metric
U3: AD9361; bga-100_10_10_1p32_0p8
X3: SiT1602B; Oscillator_SMD_ECS_2520MV-xxx-xx-4Pin_2.5x2.0mm

Connections:
+1V8: C135.1, X3.4 (VDD)
EXT_SYNC: J14.1, R68.1
GND: C80.1, C83.1, C84.1, C85.1, C86.1, C87.1, C88.1, C135.2, FL1.5 (GND), FL1.6 (GND), FL2.5 (GND), FL2.6 (GND), FL3.5 (GND), FL3.6 (GND), FL4.5 (GND), FL4.6 (GND), J5.2 (Ext), J6.2 (Ext), J7.2 (Ext), J8.2 (Ext), J9.2 (Ext), J12.2 (Ext), R18.2, U3.C1 (RX2C-), U3.D1 (RX2C+), U3.E1 (RX2B+), U3.F1 (RX2B-), U3.G7 (RX_FRAME-), U3.G10 (FB_CLK-), U3.H1 (RX1B+), U3.H9 (TX_FRAME-), U3.J1 (RX1B-), U3.K1 (RX1C+), U3.L1 (RX1C-), X3.2 (GND)
LDO_EN: R64.2
unnamed: C17.1, J9.1 (In)
unnamed: C17.2, U3.A12 (TX_EXT_LO_IN)
unnamed: C20.1, J12.1 (In)
unnamed: C20.2, U3.G1 (RX_EXT_LO_IN)
unnamed: C44.2, L3.2, U3.M8 (TX1A-)
unnamed: C45.2, L2.2, U3.M7 (TX1A+)
unnamed: C46.2, L4.2, U3.A8 (TX2A+)
unnamed: C47.2, L5.2, U3.A7 (TX2A-)
unnamed: C80.2, C81.2, U3.M12 (XTALN)
unnamed: C83.2, C87.2, C88.2, FB9.2, L4.1, L5.1, U3.A9 (TX2B-), U3.A10 (TX2B+)
unnamed: C84.2, C85.2, C86.2, FB1.2, L2.1, L3.1, U3.M9 (TX1B+), U3.M10 (TX1B-)
unnamed: C107.2, U3.M1 (RX1A+)
unnamed: C108.2, U3.M2 (RX1A-)
unnamed: C115.2, U3.A2 (RX2A+)
unnamed: C116.2, U3.A1 (RX2A-)
unnamed: FL1.1 (UBP), J5.1 (In)
unnamed: FL2.1 (UBP), J6.1 (In)
unnamed: FL3.1 (UBP), J7.1 (In)
unnamed: FL4.1 (UBP), J8.1 (In)
unnamed: R64.1, X3.1 (Tri-State)
unnamed: R67.2, R68.2, U3.H5 (SYNC_IN)
TRANS_AUX_ADC: U3.L5 (AUXADC)
TRANS_AUX_DAC1: U3.B3 (AUXDAC1)
TRANS_AUX_DAC2: U3.C3 (AUXDAC2)
TRANS_CMOS_FB_CLK: U3.F10 (FB_CLK+)
TRANS_CMOS_RX_D0: U3.K11 (P1_D0/RX_D0-)
TRANS_CMOS_RX_D1: U3.J12 (P1_D1/RX_D0+)
TRANS_CMOS_RX_D2: U3.K10 (P1_D2/RX_D1-)
TRANS_CMOS_RX_D3: U3.J11 (P1_D3/RX_D1+)
TRANS_CMOS_RX_D4: U3.K9 (P1_D4/RX_D2-)
TRANS_CMOS_RX_D5: U3.J10 (P1_D5/RX_D2+)
TRANS_CMOS_RX_D6: U3.K8 (P1_D6/RX_D3-)
TRANS_CMOS_RX_D7: U3.J9 (P1_D7/RX_D3+)
TRANS_CMOS_RX_D8: U3.K7 (P1_D8/RX_D4-)
TRANS_CMOS_RX_D9: U3.J8 (P1_D9/RX_D4+)
TRANS_CMOS_RX_D10: U3.J7 (P1_D10/RX_D5-)
TRANS_CMOS_RX_D11: U3.H8 (P1_D11/RX_D5+)
TRANS_CMOS_RX_FRAME: U3.G8 (RX_FRAME+)
TRANS_CMOS_TX_D0: U3.E12 (P0_D0/TX_D0-)
TRANS_CMOS_TX_D1: U3.D11 (P0_D1/TX_D0+)
TRANS_CMOS_TX_D2: U3.E11 (P0_D2/TX_D1-)
TRANS_CMOS_TX_D3: U3.D10 (P0_D3/TX_D1+)
TRANS_CMOS_TX_D4: U3.E10 (P0_D4/TX_D2-)
TRANS_CMOS_TX_D5: U3.D9 (P0_D5/TX_D2+)
TRANS_CMOS_TX_D6: U3.E9 (P0_D6/TX_D3-)
TRANS_CMOS_TX_D7: U3.D8 (P0_D7/TX_D3+)
TRANS_CMOS_TX_D8: U3.E8 (P0_D8/TX_D4-)
TRANS_CMOS_TX_D9: U3.D7 (P0_D9/TX_D4+)
TRANS_CMOS_TX_D10: U3.F8 (P0_D10/TX_D5-)
TRANS_CMOS_TX_D11: U3.E7 (P0_D11/TX_D5+)
TRANS_CMOS_TX_FRAME: U3.G9 (TX_FRAME+)
TRANS_CTRL_IN0: U3.C5 (CTRL_IN0)
TRANS_CTRL_IN1: U3.C6 (CTRL_IN1)
TRANS_CTRL_IN2: U3.D6 (CTRL_IN2)
TRANS_CTRL_IN3: U3.D5 (CTRL_IN3)
TRANS_CTRL_OUT0: U3.D4 (CTRL_OUT0)
TRANS_CTRL_OUT1: U3.E4 (CTRL_OUT1)
TRANS_CTRL_OUT2: U3.E5 (CTRL_OUT2)
TRANS_CTRL_OUT3: U3.E6 (CTRL_OUT3)
TRANS_CTRL_OUT4: U3.F6 (CTRL_OUT4)
TRANS_CTRL_OUT5: U3.F5 (CTRL_OUT5)
TRANS_CTRL_OUT6: U3.F4 (CTRL_OUT6)
TRANS_CTRL_OUT7: U3.G4 (CTRL_OUT7)
TRANS_ENABLE: U3.G6 (ENABLE)
TRANS_ENAGC: U3.G5 (EN_AGC)
TRANS_GPO_0: U3.B7 (GPO_0)
TRANS_GPO_1: U3.B6 (GPO_1)
TRANS_GPO_2: U3.B5 (GPO_2)
TRANS_GPO_3: U3.B4 (GPO_3)
TRANS_MRCC_CLKOUT: U3.J6 (CLK_OUT)
TRANS_MRCC_DATA_CLK: U3.G11 (DATA_CLK+)
TRANS_OSC_N: C81.1, X3.3 (OUT)
TRANS_RBIAS: R18.1, U3.L4 (RBIAS)
TRANS_RST: U3.K5 (~RESET)
TRANS_RXRF0_N: C108.1, FL3.3 (RF_N)
TRANS_RXRF0_P: C107.1, FL3.4 (RF_P)
TRANS_RXRF1_N: C116.1, FL4.3 (RF_N)
TRANS_RXRF1_P: C115.1, FL4.4 (RF_P)
TRANS_SPI_CLK: U3.J5 (SPI_CLK)
TRANS_SPI_MISO: U3.L6 (SPI_MISO)
TRANS_SPI_MOSI: U3.J4 (SPI_MOSI)
TRANS_SPI_SS: U3.K6 (SPI_~EN)
TRANS_SYNC: R67.1
TRANS_TXNRX: U3.H4 (TX~RX)
TRANS_TXRF0_N: C44.1, FL1.4 (RF_P)
TRANS_TXRF0_P: C45.1, FL1.3 (RF_N)
TRANS_TXRF1_N: C47.1, FL2.4 (RF_P)
TRANS_TXRF1_P: C46.1, FL2.3 (RF_N)
VCC_1V3_TRANS_0: FB1.1
VCC_1V3_TRANS_1: FB9.1

Notes on the sheet:
Feedback Clock. These pins receive the FB_CLK signal that clocks in TX data. In CMOS mode, use FB_CLK_P as the input and tie FB_CLK_N to ground.
Receive Data Clock Output. These pins transmit the DATA_CLK signal that is used by the BBP to clock RX data. In CMOS mode, use DATA_CLK_P as the output and leave DATA_CLK_N unconnected.
