john-luan/SDR-dongle/hardware/USB_Connector.kicad_sch

## KiCad design hardware/USB_Connector.kicad_sch (2022-02-24)

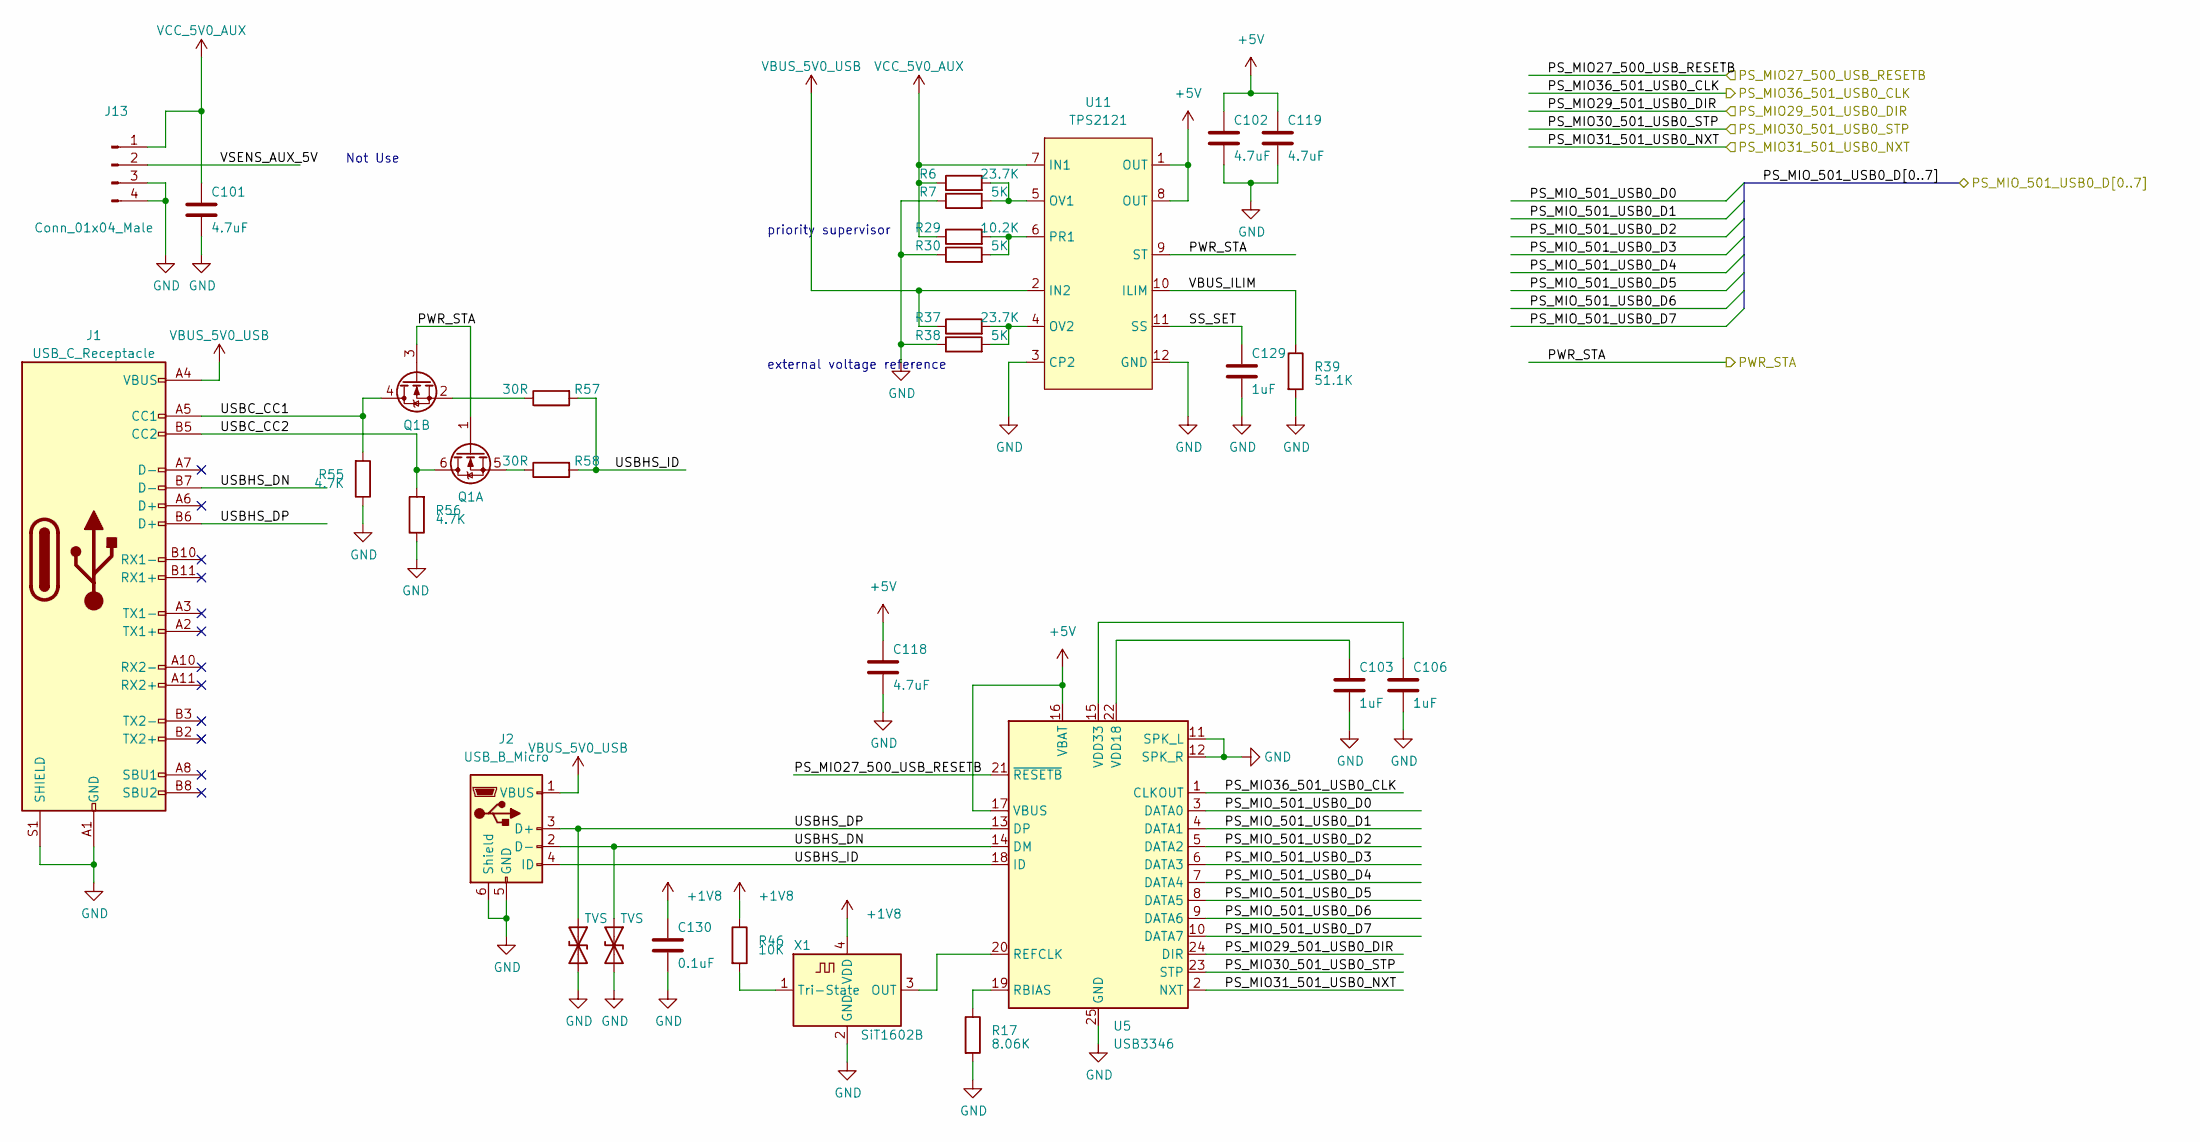
[picture p31: schematic USB_Connector.kicad_sch]

Parts:
C101, C102, C118, C119: 4.7uF; C_0402_1005Metric
C103, C106, C129: 1uF; C_0402_1005Metric
C130: 0.1uF; C_0201_0603Metric
D4, D5: TVS; R_0201_0603Metric
J1: USB_C_Receptacle; USB_C_Receptacle_Amphenol_12401548E4-2A_CircularHoles
J2: USB_B_Micro; USB_Micro-B_Amphenol_10104110_Horizontal
J13: Conn_01x04_Male; BM03B-ACHSS-GAN-TF
Q1: Q_Dual_NMOS_PMDXB600UNE; DFN-6-1EP_1.2x1.2mm_P0.4mm_EP0.3x0.94mm_PullBack
R6, R37: 23.7K; R_0201_0603Metric
R7, R30, R38: 5K; R_0201_0603Metric
R17: 8.06K; R_0201_0603Metric
R29: 10.2K; R_0201_0603Metric
R39: 51.1K; R_0201_0603Metric
R46: 10K; R_0201_0603Metric
R55, R56: 4.7K; R_0201_0603Metric
R57, R58: 30R; R_0201_0603Metric
U5: USB3346; QFN-24-1EP_4x4mm_P0.5mm_EP2.6x2.6mm
U11: TPS2121; VQFN-12_2p0_2p5_0p5
X1: SiT1602B; Oscillator_SMD_ECS_2520MV-xxx-xx-4Pin_2.5x2.0mm

Connections:
+1V8: C130.1, R46.1, X1.4 (VDD)
+5V: C102.1, C118.1, C119.1, U5.16 (VBAT), U5.17 (VBUS), U11.1 (OUT), U11.8 (OUT)
GND: C101.2, C102.2, C103.2, C106.2, C118.2, C119.2, C129.2, C130.2, D4.2 (A2), D5.2 (A2), J1.A1 (GND), J1.A12 (GND), J1.B1 (GND), J1.B12 (GND), J1.S1 (SHIELD), J2.5 (GND), J2.6 (Shield), J13.3, J13.4, R7.1, R17.2, R30.1, R38.1, R39.2, R55.1, R56.1, U5.11 (SPK_L), U5.12 (SPK_R), U5.25 (GND), U11.3 (CP2), U11.12 (GND), X1.2 (GND)
unnamed: C103.1, U5.22 (VDD18)
unnamed: C106.1, U5.15 (VDD33)
unnamed: Q1.2 (S), R57.1
unnamed: Q1.5 (S), R58.1
unnamed: R6.2, R7.2, U11.5 (OV1)
unnamed: R17.1, U5.19 (RBIAS)
unnamed: R29.2, R30.2, U11.6 (PR1)
unnamed: R37.2, R38.2, U11.4 (OV2)
unnamed: R46.2, X1.1 (Tri-State)
unnamed: U5.20 (REFCLK), X1.3 (OUT)
PS_MIO27_500_USB_RESETB: U5.21 (~RESETB)
PS_MIO29_501_USB0_DIR: U5.24 (DIR)
PS_MIO30_501_USB0_STP: U5.23 (STP)
PS_MIO31_501_USB0_NXT: U5.2 (NXT)
PS_MIO36_501_USB0_CLK: U5.1 (CLKOUT)
PS_MIO_501_USB0_D0: U5.3 (DATA0)
PS_MIO_501_USB0_D1: U5.4 (DATA1)
PS_MIO_501_USB0_D2: U5.5 (DATA2)
PS_MIO_501_USB0_D3: U5.6 (DATA3)
PS_MIO_501_USB0_D4: U5.7 (DATA4)
PS_MIO_501_USB0_D5: U5.8 (DATA5)
PS_MIO_501_USB0_D6: U5.9 (DATA6)
PS_MIO_501_USB0_D7: U5.10 (DATA7)
PWR_STA: Q1.1 (G), Q1.3 (G), U11.9 (ST)
SS_SET: C129.1, U11.11 (SS)
USBC_CC1: J1.A5 (CC1), Q1.4 (D), R55.2
USBC_CC2: J1.B5 (CC2), Q1.6 (D), R56.2
USBHS_DN: D5.1 (A1), J1.B7 (D-), J2.2 (D-), U5.14 (DM)
USBHS_DP: D4.1 (A1), J1.B6 (D+), J2.3 (D+), U5.13 (DP)
USBHS_ID: J2.4 (ID), R57.2, R58.2, U5.18 (ID)
VBUS_5V0_USB: J1.A4 (VBUS), J1.A9 (VBUS), J1.B4 (VBUS), J1.B9 (VBUS), J2.1 (VBUS), R37.1, U11.2 (IN2)
VBUS_ILIM: R39.1, U11.10 (ILIM)
VCC_5V0_AUX: C101.1, J13.1, R6.1, R29.1, U11.7 (IN1)
VSENS_AUX_5V: J13.2

Notes on the sheet:
external voltage reference
Not Use
priority supervisor
