john-luan/SDR-dongle/hardware/zynq_sdr_dongle.kicad_sch

## KiCad design hardware/zynq_sdr_dongle.kicad_sch (2022-02-24)

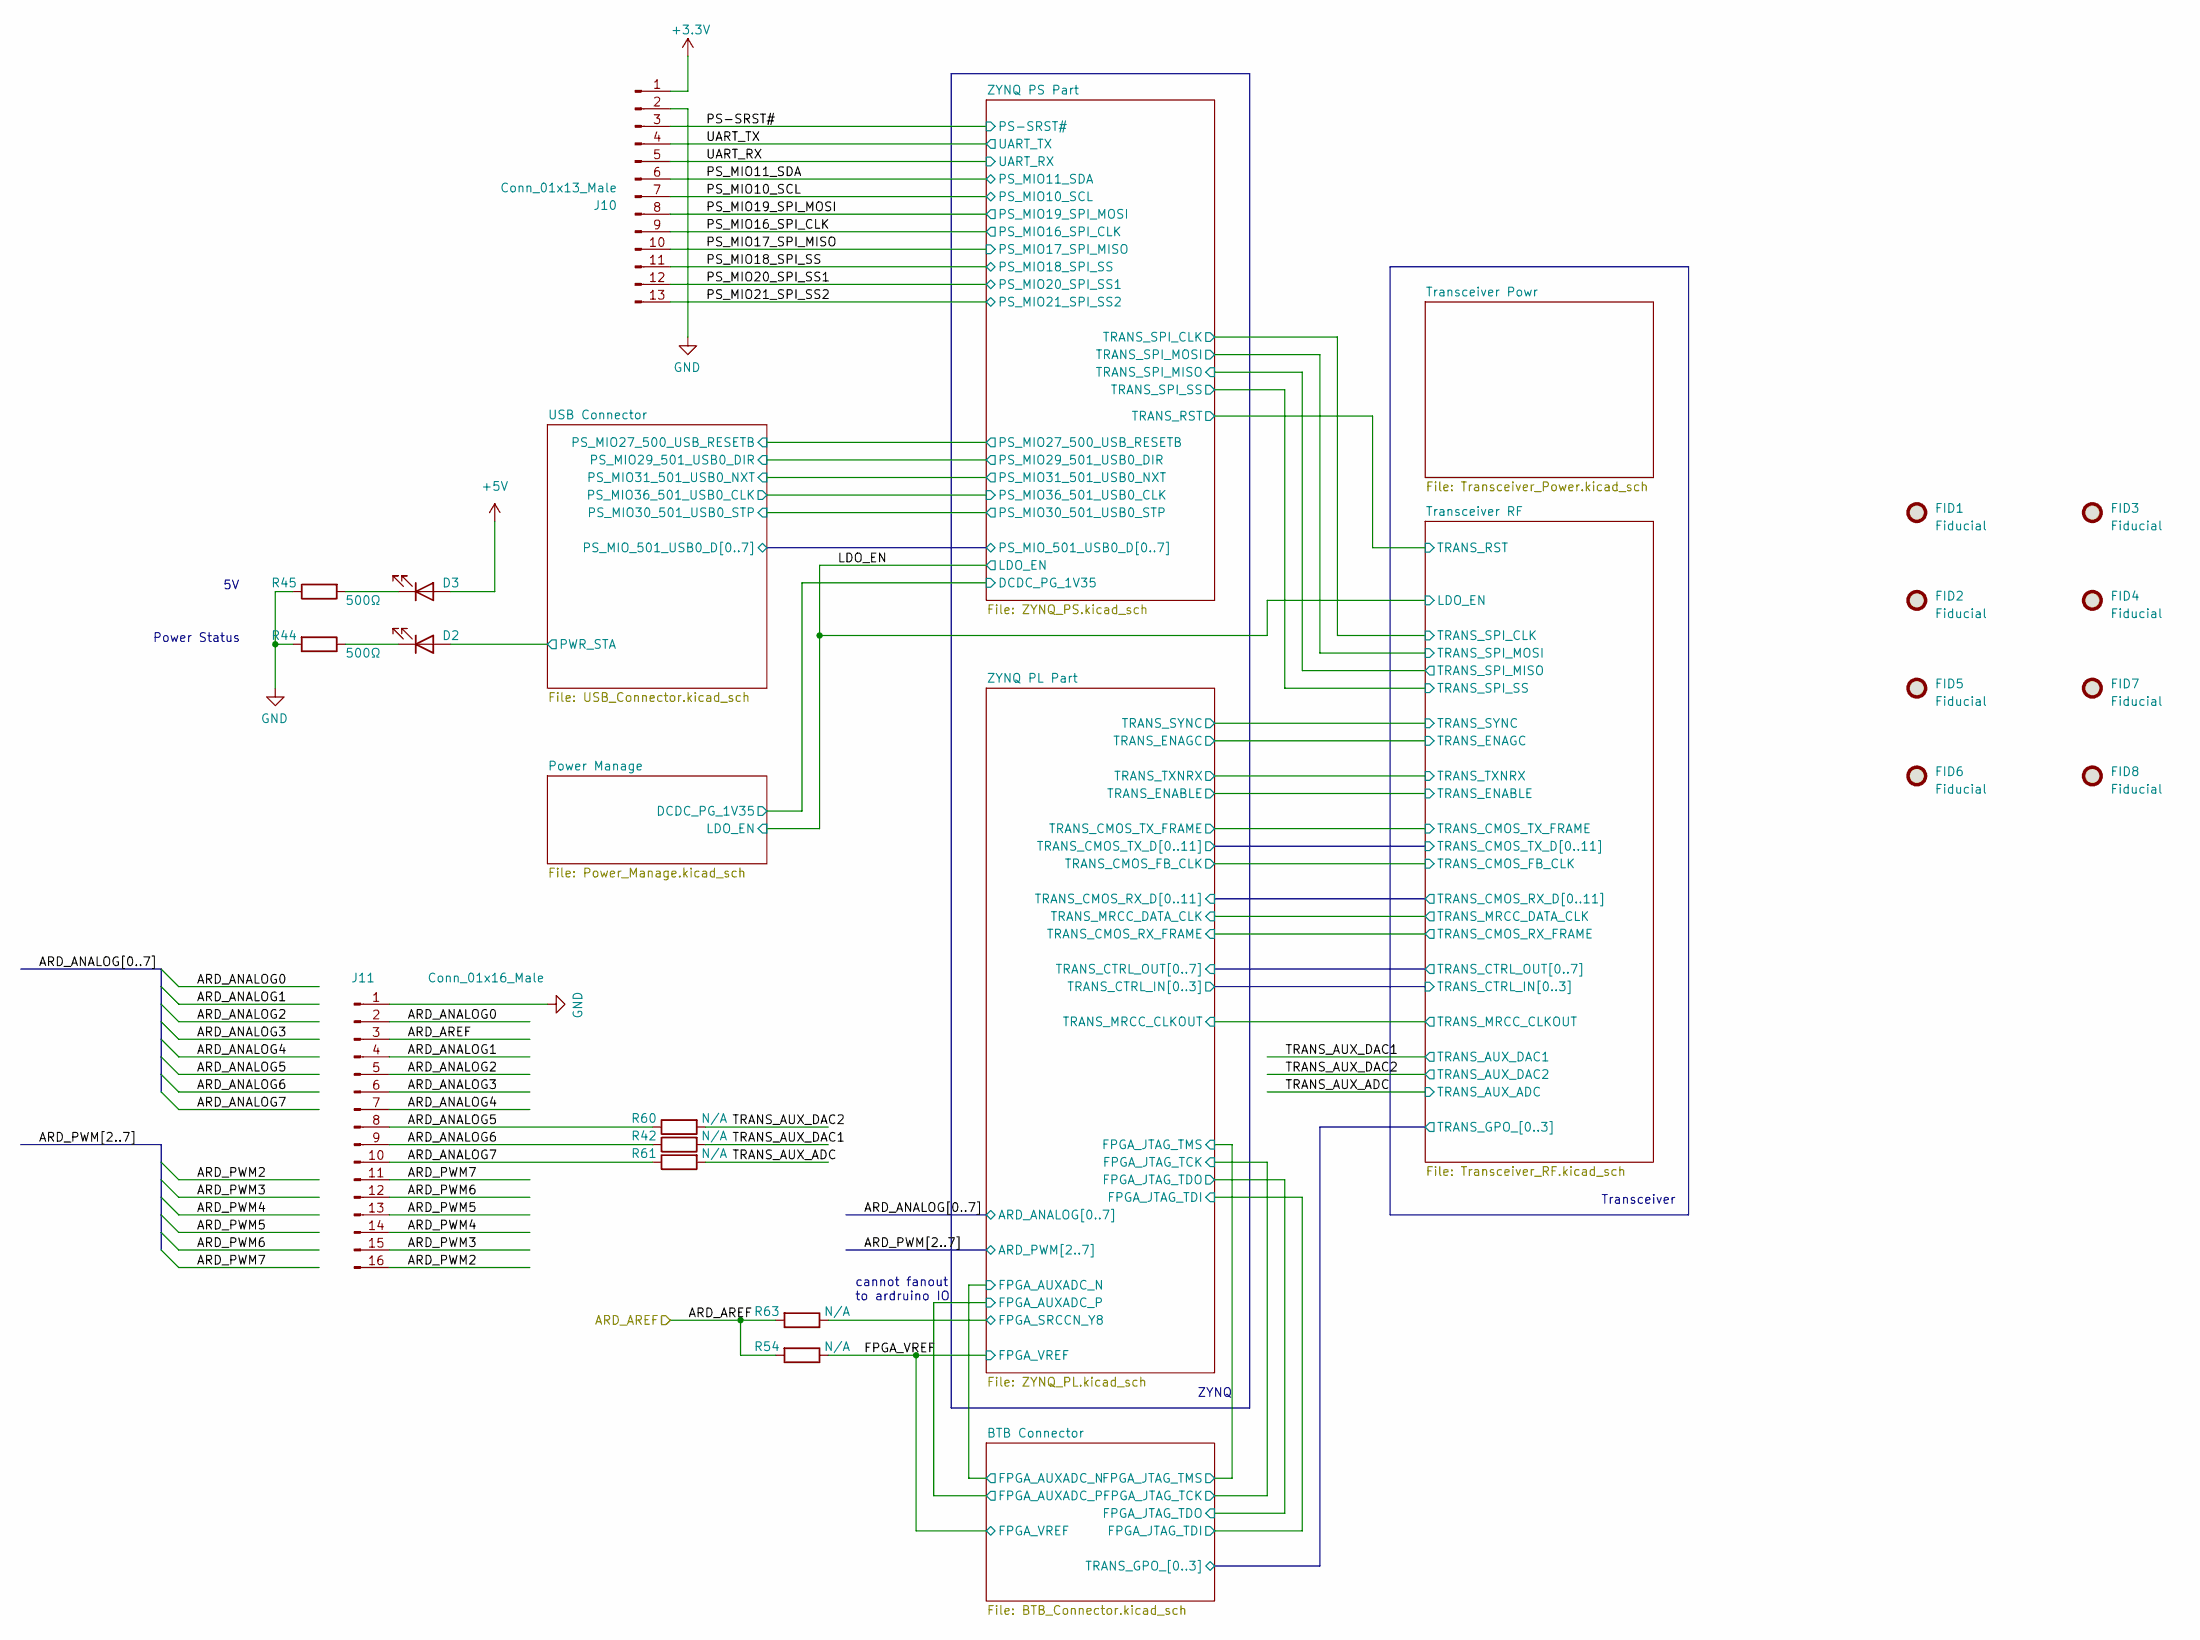
[picture p32: schematic zynq_sdr_dongle.kicad_sch]

Parts:
D2, D3: LED; LED_0201_0603Metric
FID1, FID2, FID3, FID4, FID5, FID6, FID7, FID8: Fiducial; Fiducial_0.75mm_Mask2.25mm
J10: Conn_01x13_Male; PinHeader_1x13_P2.54mm_Vertical
J11: Conn_01x16_Male; PinHeader_1x16_P2.54mm_Vertical
R42, R54, R60, R61, R63: N/A; R_0201_0603Metric
R44, R45: 500Ω; R_0201_0603Metric

Connections:
+3.3V: J10.1
+5V: D3.2 (A)
ARD_ANALOG0: J11.2
ARD_ANALOG1: J11.4
ARD_ANALOG2: J11.5
ARD_ANALOG3: J11.6
ARD_ANALOG4: J11.7
ARD_ANALOG5: J11.8, R60.1
ARD_ANALOG6: J11.9, R42.1
ARD_ANALOG7: J11.10, R61.1
ARD_AREF: J11.3, R54.2, R63.2
ARD_PWM2: J11.16
ARD_PWM3: J11.15
ARD_PWM4: J11.14
ARD_PWM5: J11.13
ARD_PWM6: J11.12
ARD_PWM7: J11.11
FPGA_SRCCN_Y8: R63.1
FPGA_VREF: R54.1
GND: J10.2, J11.1, R44.2, R45.1
unnamed: D2.1 (K), R44.1
unnamed: D3.1 (K), R45.2
PS-SRST#: J10.3
PS_MIO10_SCL: J10.7
PS_MIO11_SDA: J10.6
PS_MIO16_SPI_CLK: J10.9
PS_MIO17_SPI_MISO: J10.10
PS_MIO18_SPI_SS: J10.11
PS_MIO19_SPI_MOSI: J10.8
PS_MIO20_SPI_SS1: J10.12
PS_MIO21_SPI_SS2: J10.13
PWR_STA: D2.2 (A)
TRANS_AUX_ADC: R61.2
TRANS_AUX_DAC1: R42.2
TRANS_AUX_DAC2: R60.2
UART_RX: J10.5
UART_TX: J10.4

Notes on the sheet:
Transceiver
ZYNQ
cannot fanout to ardruino IO
Power Status
